pricem/da_platform/notes/ztex_pinout_aug16.xlsx

Sheet: v1
Iso interface pin name | Nexys2 port | ZTEX breakout pin | ZTEX FPGA pin
mclk | pmod3[1] | C24 | M4
amcs | pmod3[0] | C23 | N4
amdi | pmod3[2] | C25 | M3
amdo | pmod3[3] | C26 | M2
dmcs | pmod4[0] | C27 | K5
dmdi | pmod4[1] | C28 | L4
dmdo | pmod4[2] | C29 | L3
dirchan | pmod4[3] | C30 | K3
acon1 | pmod3[6] | D25 | R2
acon0 | pmod3[7] | D26 | P2
aovf | pmod3[5] | D24 | R1
clk0 | pmod4[4] | D27 | N2
reset_out | pmod4[7] | D30 | L1
srclk | pmod4[6] | D29 | M1
clksel | pmod4[5] | D28 | N1
clk1 | pmod3[4] | D23 | T1
slotdata1[5] | pmod2[0] | C19 | N6
slotdata1[4] | pmod2[1] | C20 | M6
slotdata1[3] | pmod1[2] | C14 | U2
slotdata1[2] | pmod1[3] | C15 | K6
slotdata1[1] | pmod1[0] | C12 | R5
slotdata1[0] | pmod1[1] | C13 | V2
slotdata0[5] | pmod2[5] | D20 | N5
slotdata0[4] | pmod2[4] | D19 | P5
slotdata0[3] | pmod1[7] | D15 | R3
slotdata0[2] | pmod1[6] | D14 | T3
slotdata0[1] | pmod1[5] | D13 | U1
slotdata0[0] | pmod1[4] | D12 | V1
slotdata3[5] |  | C6 | U6 | Unused signals
slotdata3[4] |  | D6 | V5
slotdata3[3] |  | C7 | T8
slotdata3[2] |  | D7 | V4
slotdata3[1] |  | C8 | R8
slotdata3[0] |  | D8 | T5
slotdata2[5] |  | C9 | R7
slotdata2[4] |  | D9 | T4
slotdata2[3] |  | C10 | T6
slotdata2[2] |  | D10 | U4
slotdata2[1] |  | C11 | R6
slotdata2[0] |  | D11 | U3
led_debug[3] |  | D4 | V7
led_debug[2] |  | C4 | U8
led_debug[1] |  | D3 | V9
led_debug[0] |  | C3 | U9
Notes:
- Make clk0/CLK1 clock capable

Sheet: v2
OLD pin name | OLD breakout pin | ALT pin name | ALT2 pin name | Iso interface pin name | Carrier conn pin | ZTEX breakout pin | ZTEX FPGA pin | Requirements
slotdata0[3] | D15 | slotdata0[1] | slotdata[1] | s0_lrck | 1 | A28 | B12
slotdata0[5] | D20 | slotdata0[0] | slotdata[0] | s0_bck | 2 | B28 | C12
 |  | slotdata0[3] | slotdata[3] | s0_d1 | 3 | A27 | B14
slotdata0[4] | D19 | slotdata0[2] | slotdata[2] | s0_d0 | 4 | B27 | B13
 |  | slotdata0[5] | slotdata[5] | s0_d3 | 5 | A26 | A16
 |  | slotdata0[4] | slotdata[4] | s0_d2 | 6 | B26 | A15
slotdata1[3] | C14 | slotdata1[1] | slotdata[7] | s1_lrck | 9 | A24 | C14 |  | OK
slotdata1[5] | C19 | slotdata1[0] | slotdata[6] | s1_bck | 10 | B24 | D14 |  | OK
 |  | slotdata1[3] | slotdata[9] | s1_d1 | 11 | A23 | B17
slotdata1[4] | C20 | slotdata1[2] | slotdata[8] | s1_d0 | 12 | B23 | B16 |  | OK
 |  | slotdata1[5] | slotdata[11] | s1_d3 | 13 | A22 | C15
 |  | slotdata1[4] | slotdata[10] | s1_d2 | 14 | B22 | D15
 |  | slotdata2[1] | slotdata[13] | s2_lrck | 17 | A20 | C17
 |  | slotdata2[0] | slotdata[12] | s2_bck | 18 | B20 | C16
 |  | slotdata2[3] | slotdata[15] | s2_d1 | 19 | A19 | E16
 |  | slotdata2[2] | slotdata[14] | s2_d0 | 20 | B19 | E15
 |  | slotdata2[5] | slotdata[17] | s2_d3 | 21 | A18 | F13
 |  | slotdata2[4] | slotdata[16] | s2_d2 | 22 | B18 | F14
 |  | slotdata3[1] | slotdata[19] | s3_lrck | 25 | A14 | G13
 |  | slotdata3[0] | slotdata[18] | s3_bck | 26 | B14 | D17
 |  | slotdata3[3] | slotdata[21] | s3_d1 | 27 | A13 | D18
 |  | slotdata3[2] | slotdata[20] | s3_d0 | 28 | B13 | E17
 |  | slotdata3[5] | slotdata[23] | s3_d3 | 29 | A12 | E18
 |  | slotdata3[4] | slotdata[22] | s3_d2 | 30 | B12 | F15
 |  |  |  | hwflag | 33 | A11 | F18
 |  |  |  | hwcon | 34 | B11 | F16
dmcs | C27 |  |  | cs_n | 35 | A9 | G17 |  | OK
dirchan | C30 |  |  | dirchan | 36 | B9 | G16 |  | OK
 |  |  |  | srclk2 | 37 | A8 | H17
srclk | D29 |  |  | srclk | 38 | B8 | G14 |  | OK
dmdi | C28 |  |  | mosi | 39 | A7 | J14 |  | OK - needed fix
dmdo | C29 |  |  | miso | 40 | B7 | H14 |  | OK
clksel | D28 |  |  | clksel | 42 | B6 | J13 |  | OK
mclk | C24 |  |  | sclk | 43 | A5 | J15 |  | OK - needed fix
reset_out | D30 |  |  | reset_n | 44 | B5 | K13 |  | OK
clk0 | D27 |  |  | mclk | 47 | B10 | H16 | CC | OK
 |  |  |  |  | Note: increasing pin number on carrier -> increasing number on FPGA

Sheet: v2 (before fix)
Iso interface pin name | Carrier connector pin | ZTEX breakout pin | ZTEX FPGA pin | Requirements
s0_lrck | 1 | D5
s0_bck | 2 | C5
s0_d1 | 3 | D6
s0_d0 | 4 | C6
s0_d3 | 5 | D7
s0_d2 | 6 | C7
s1_lrck | 9 | D9
s1_bck | 10 | C9
s1_d1 | 11 | D10
s1_d0 | 12 | C10
s1_d3 | 13 | D11
s1_d2 | 14 | C11
s2_lrck | 17 | D13
s2_bck | 18 | C13
s2_d1 | 19 | D14
s2_d0 | 20 | C14
s2_d3 | 21 | D15
s2_d2 | 22 | C15
s3_lrck | 25 | D19
s3_bck | 26 | C19
s3_d1 | 27 | D21
s3_d0 | 28 | C21
s3_d3 | 29 | D22
s3_d2 | 30 | C22
hwflag | 33 | D23
hwcon | 34 | C23
cs_n | 35 | D24
dirchan | 36 | C24
srclk2 | 37 | D25
srclk | 38 | C25
mosi | 39 | D26
miso | 40 | C26
clksel | 42 | C27
sclk | 43 | D28
reset_n | 44 | C28
mclk | 47 | D20 | N5 | CC
 | Note: increasing pin number on carrier -> increasing number on FPGA
