pricem/da_platform/docs/figures/dac8_adc8_loopback_fr.pdf

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

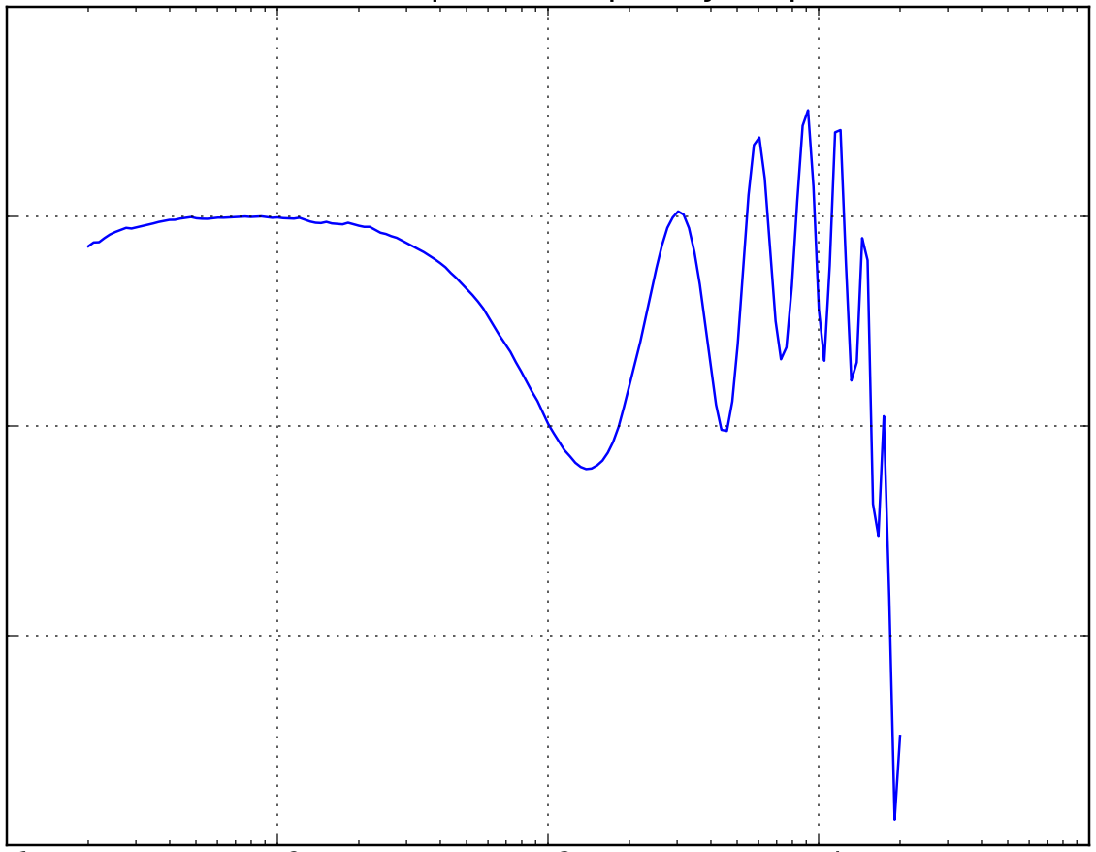
[picture p9: figure]
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
