pricem/da_platform/docs/photos/DSC_0177.JPG

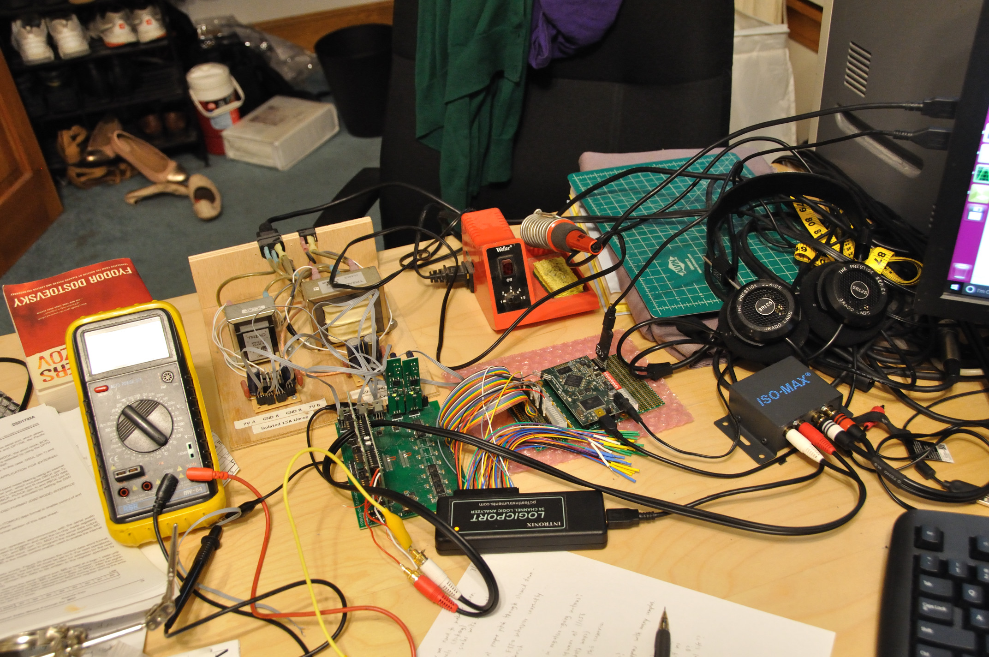
docs/photos/DSC_0177.JPG
