pricem/da_platform/docs/photos/DSC_0237.jpg

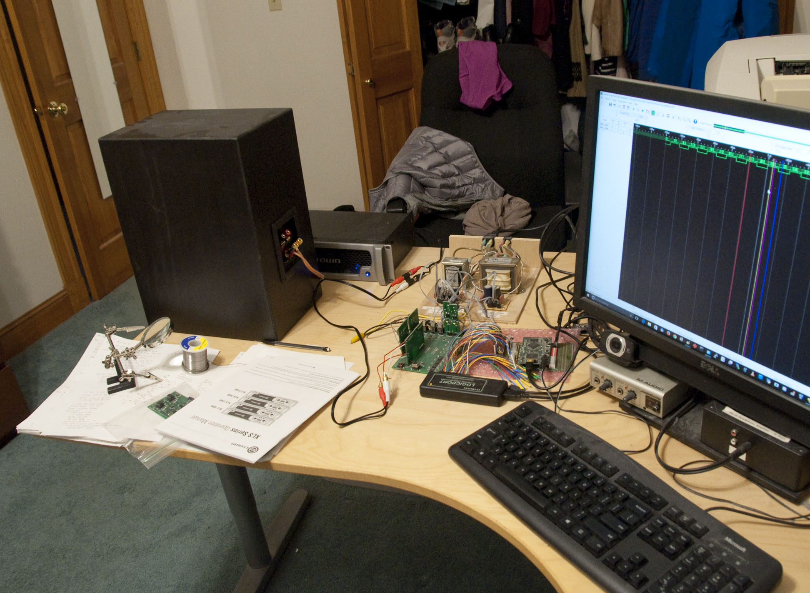
docs/photos/DSC_0237.jpg
