pricem/da_platform/docs/photos/DSC_0237_01.JPG

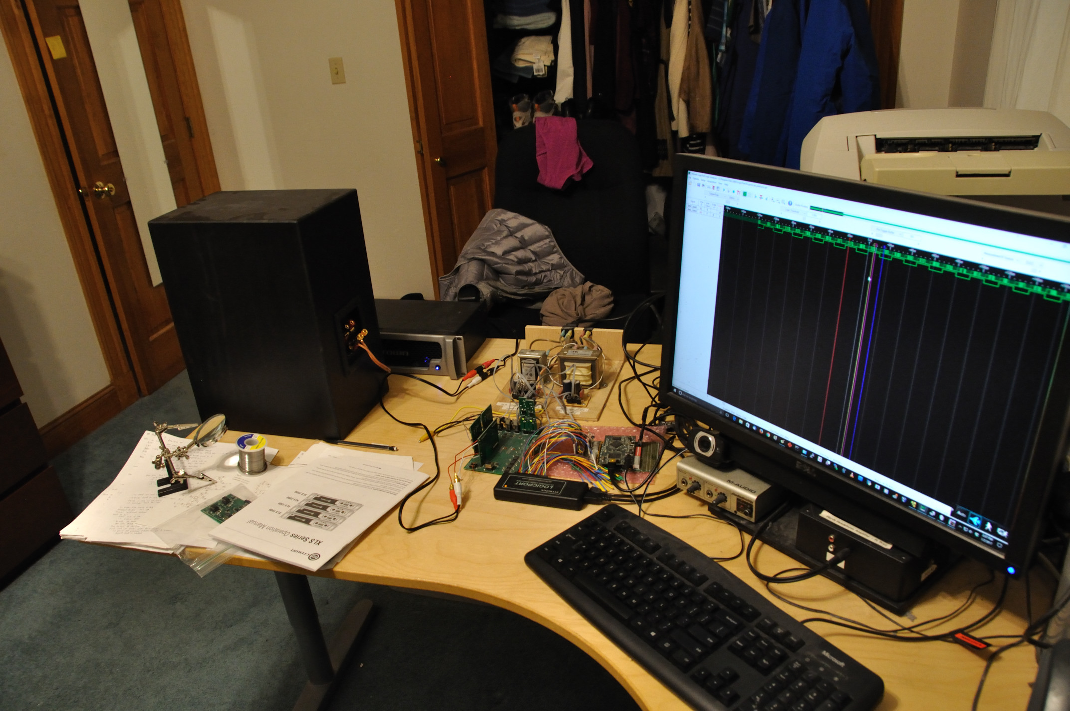
docs/photos/DSC_0237_01.JPG
