pricem/da_platform/docs/photos/DSC_0239.jpg

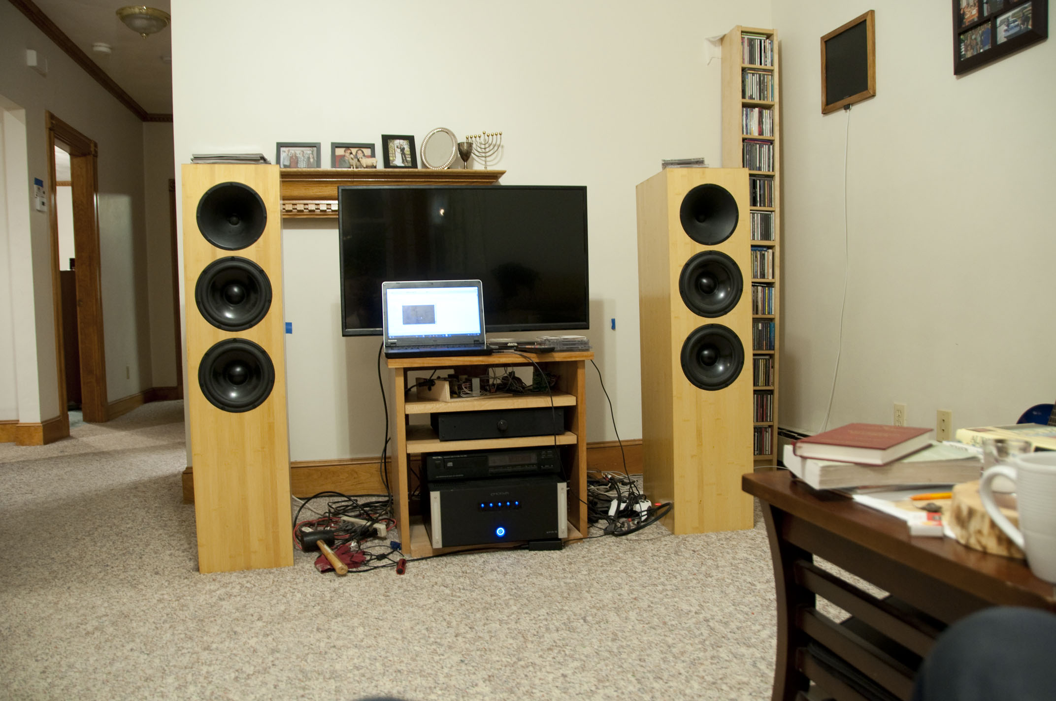
docs/photos/DSC_0239.jpg
