pricem/da_platform/docs/photos/DSC_0240.jpg

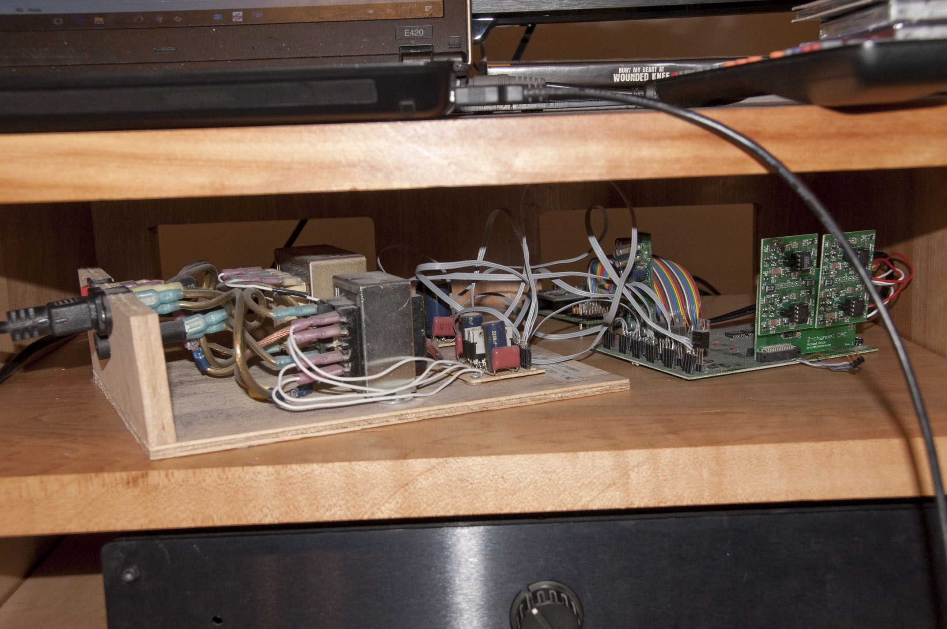
docs/photos/DSC_0240.jpg
