pricem/da_platform/docs/photos/DSC_0240_01.JPG

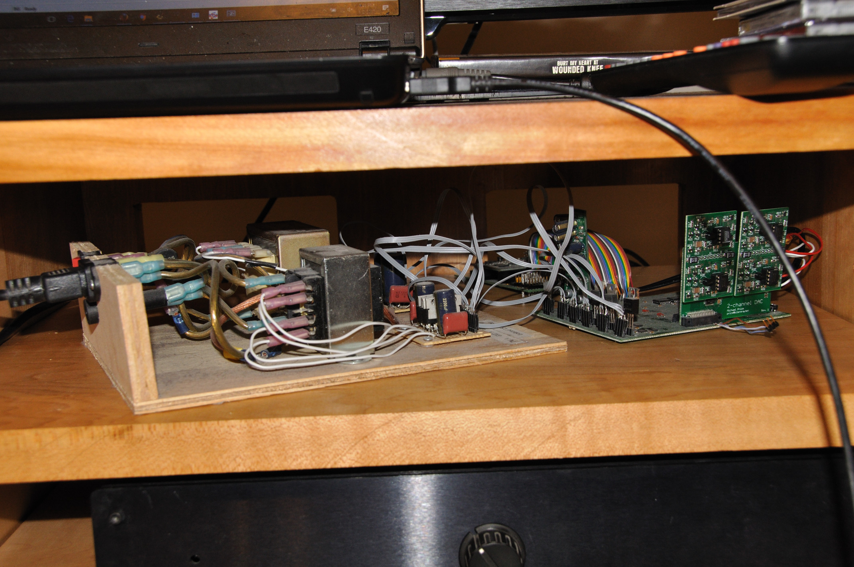
docs/photos/DSC_0240_01.JPG
