pricem/da_platform/docs/photos/DSC_0245.JPG

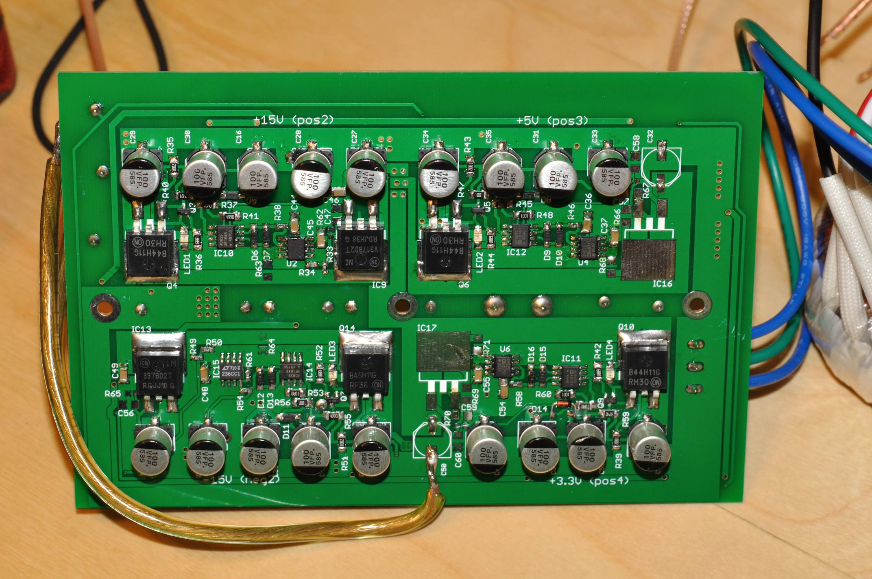
docs/photos/DSC_0245.JPG
