pricem/da_platform/docs/photos/DSC_0246.JPG

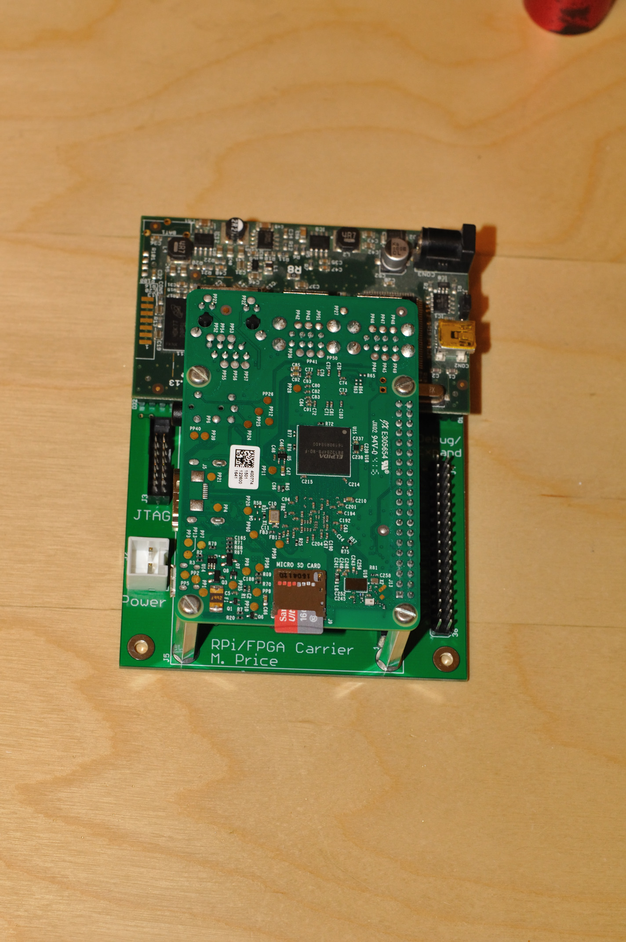
docs/photos/DSC_0246.JPG
