pricem/da_platform/docs/photos/DSC_0248.JPG

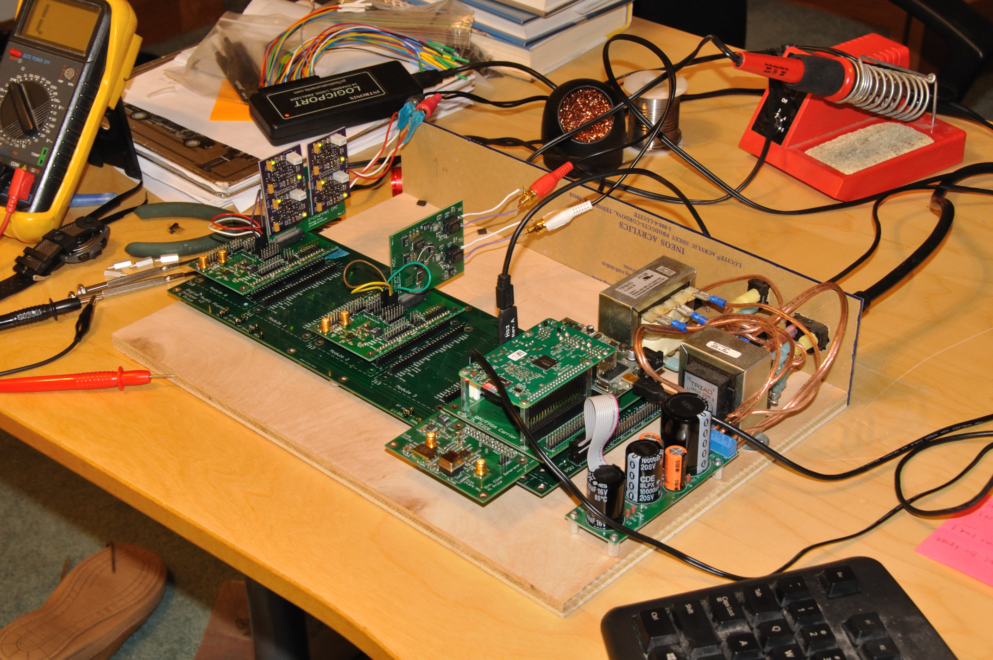
docs/photos/DSC_0248.JPG
