pricem/da_platform/docs/photos/DSC_0252_01.JPG

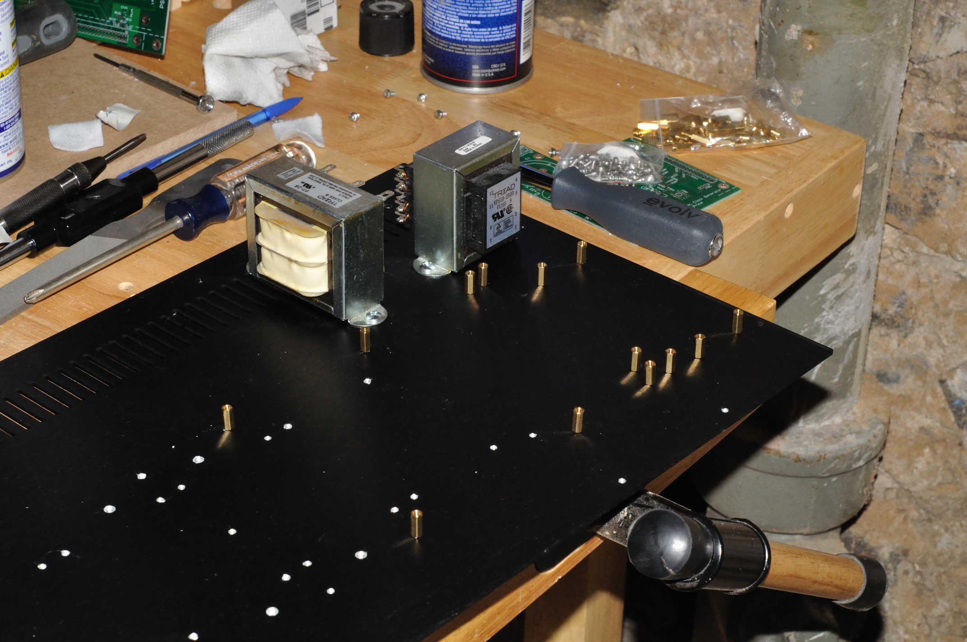
docs/photos/DSC_0252_01.JPG
