pricem/da_platform/docs/photos/DSC_0255.JPG

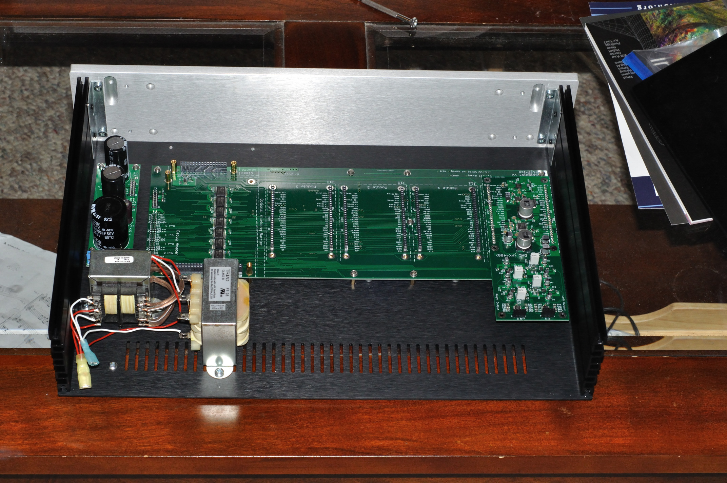
docs/photos/DSC_0255.JPG
