pricem/da_platform/docs/photos/DSC_0258.JPG

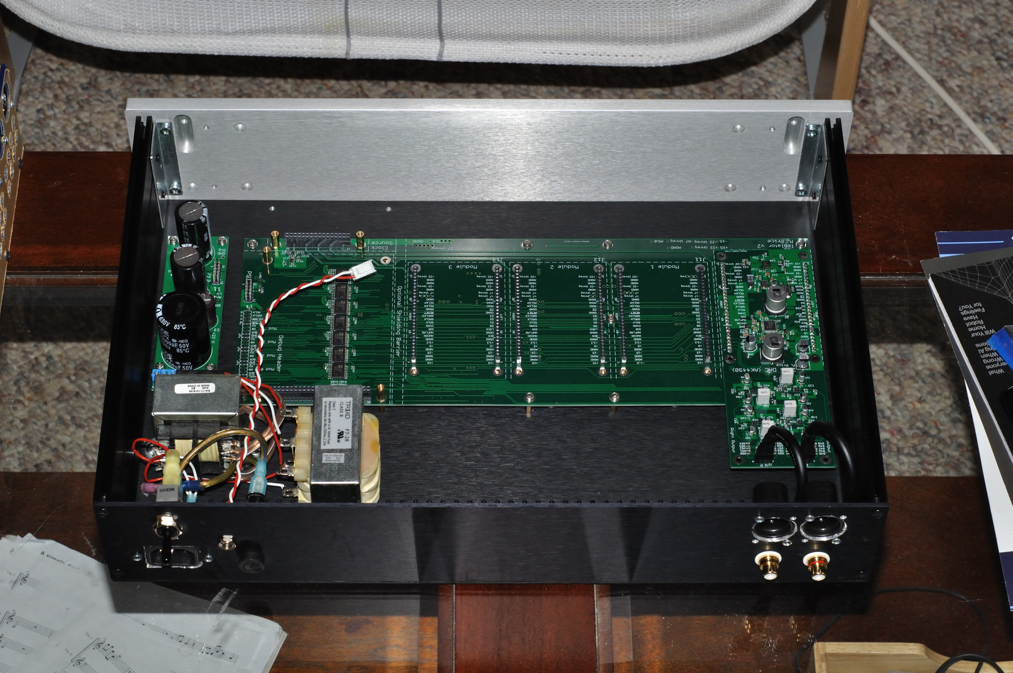
docs/photos/DSC_0258.JPG
