pricem/da_platform/docs/photos/DSC_0274.JPG

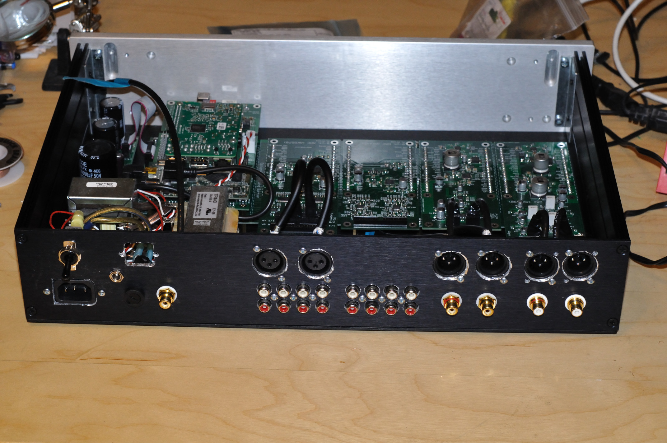
docs/photos/DSC_0274.JPG
