pricem/da_platform/docs/photos/DSC_0276.JPG

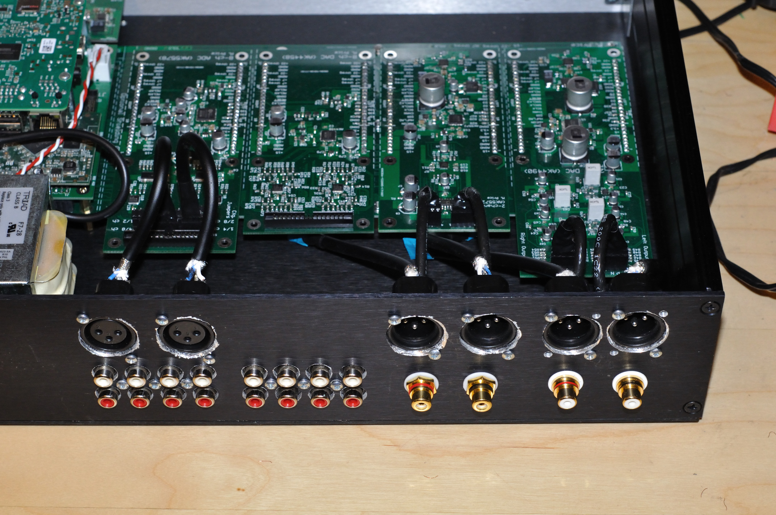
docs/photos/DSC_0276.JPG
