pricem/da_platform/docs/photos/DSC_0278.JPG

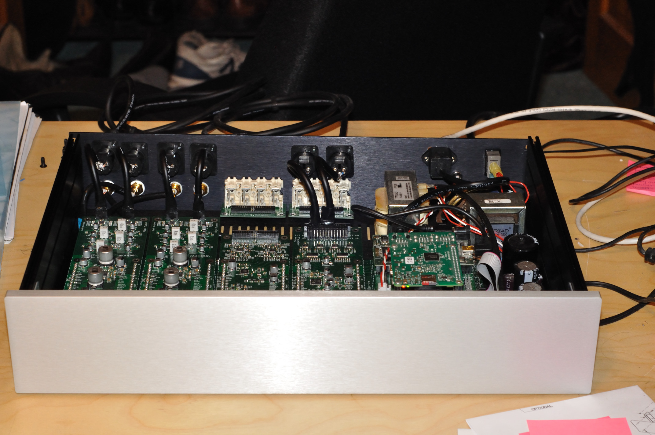
docs/photos/DSC_0278.JPG
