pricem/da_platform/docs/photos/DSC_0279.JPG

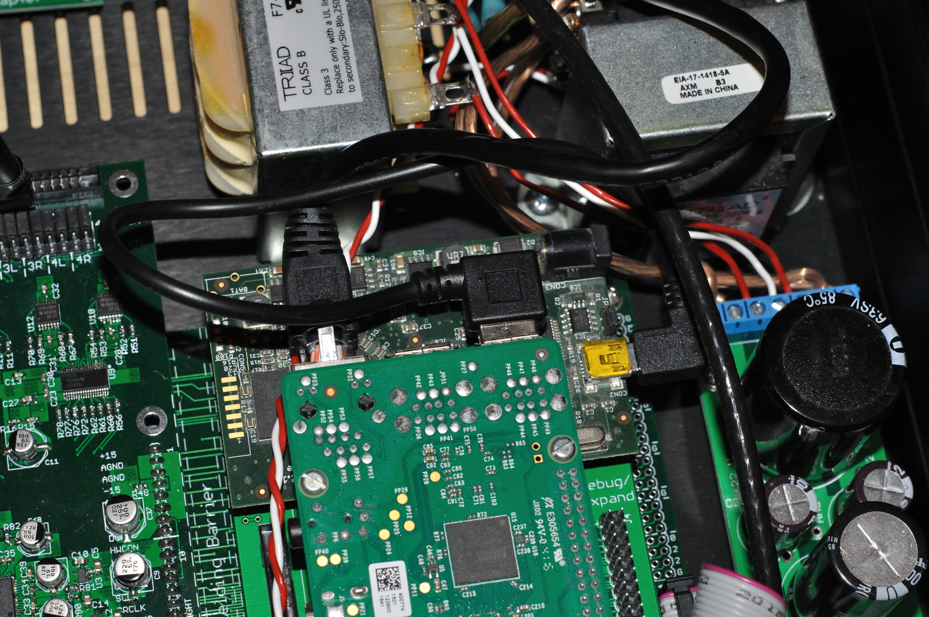
docs/photos/DSC_0279.JPG
