pricem/da_platform/docs/photos/DSC_0280.JPG

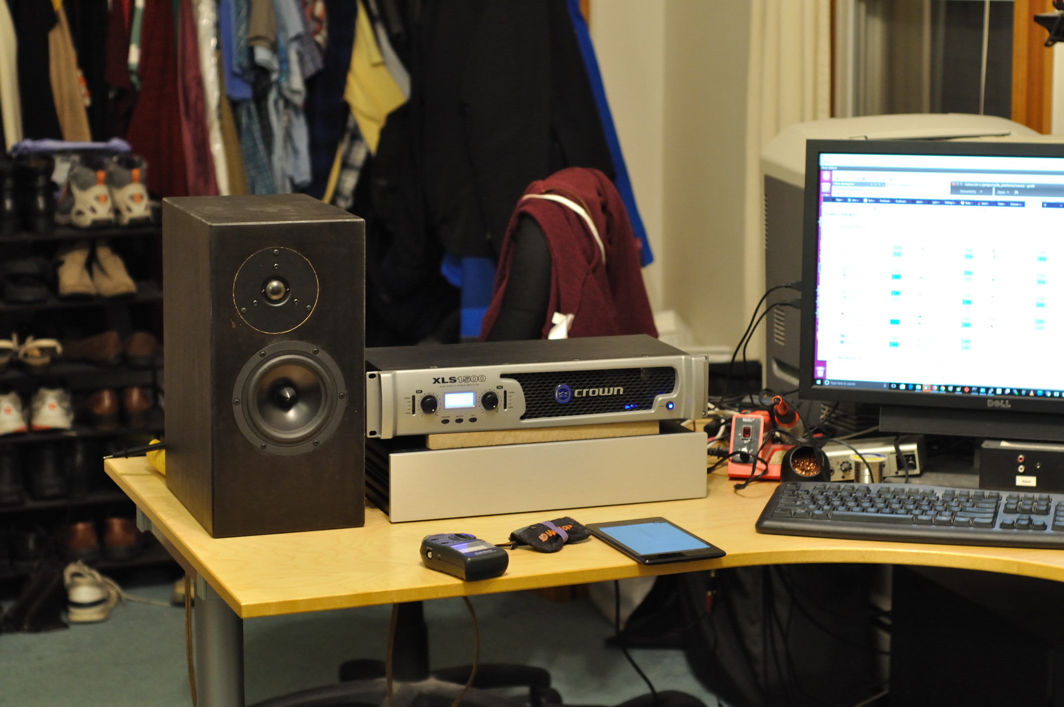
docs/photos/DSC_0280.JPG
