pricem/da_platform/docs/photos/DSC_0281.JPG

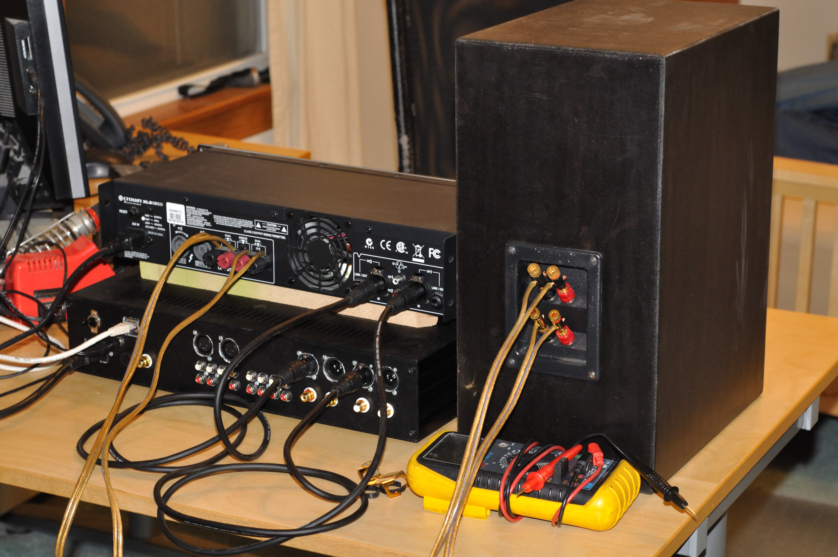
docs/photos/DSC_0281.JPG
