pricem/da_platform/docs/photos/indiv_boards/adc2_v2p1.jpg

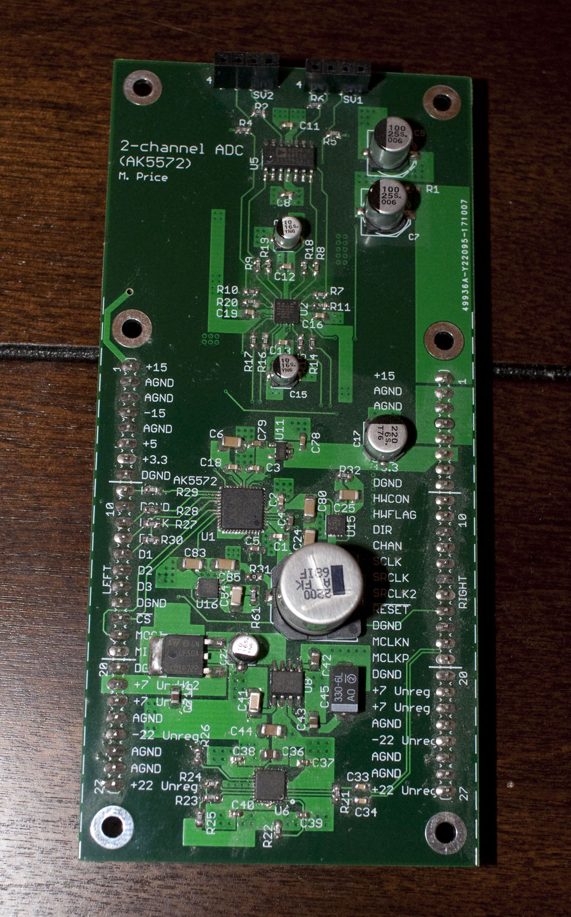
docs/photos/indiv_boards/adc2_v2p1.jpg
