pricem/da_platform/docs/photos/indiv_boards/backplane_lowcost.jpg

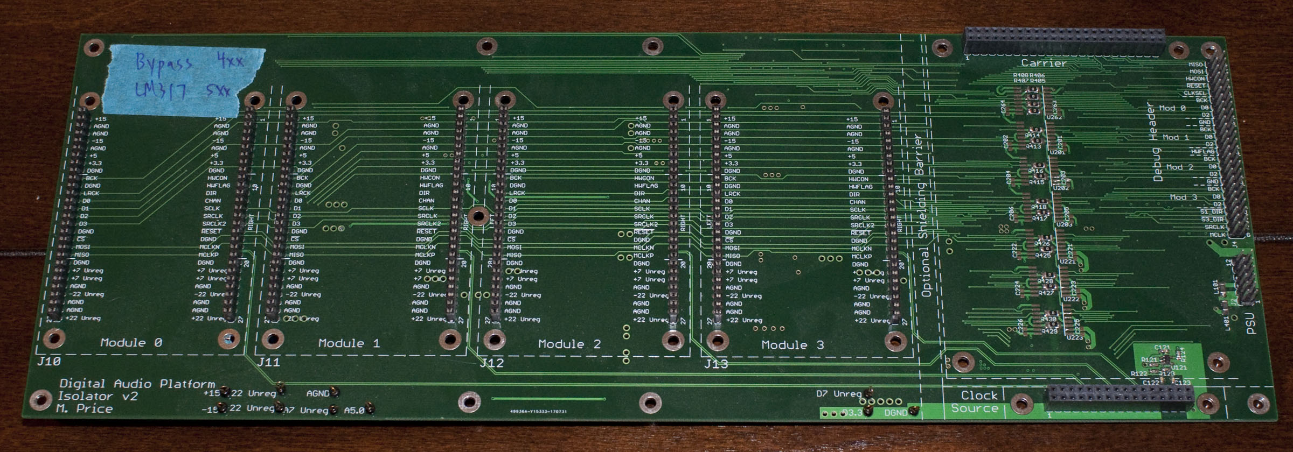
docs/photos/indiv_boards/backplane_lowcost.jpg
