pricem/da_platform/docs/schematics/dac2_v1_iv_b.pdf

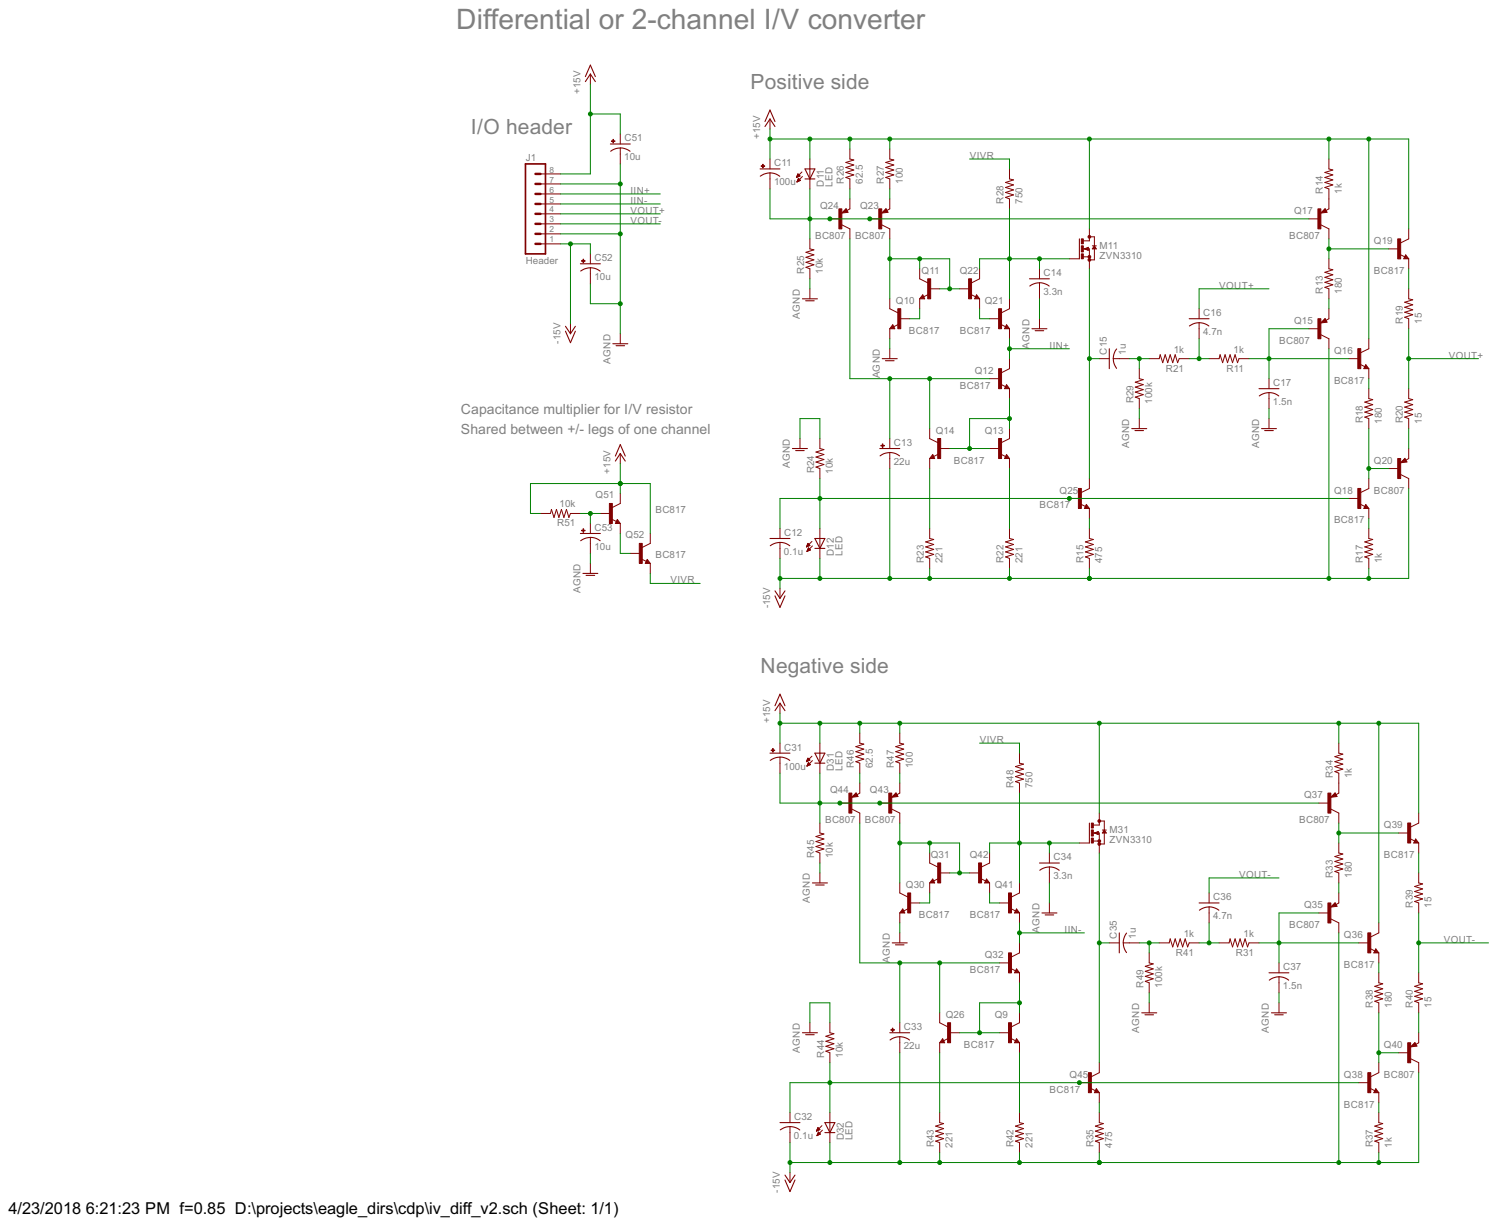
[picture p57: page 1]

Differential or 2-channel I/V converter

Capacitance multiplier for I/V resistor
Shared between +/- legs of one channel

4/23/2018 6:21:23 PM f=0.85 D:\projects\eagle_dirs\cdp\iv_diff_v2.sch (Sheet: 1/1)
