pricem/da_platform/docs/schematics/dac2_v2.pdf

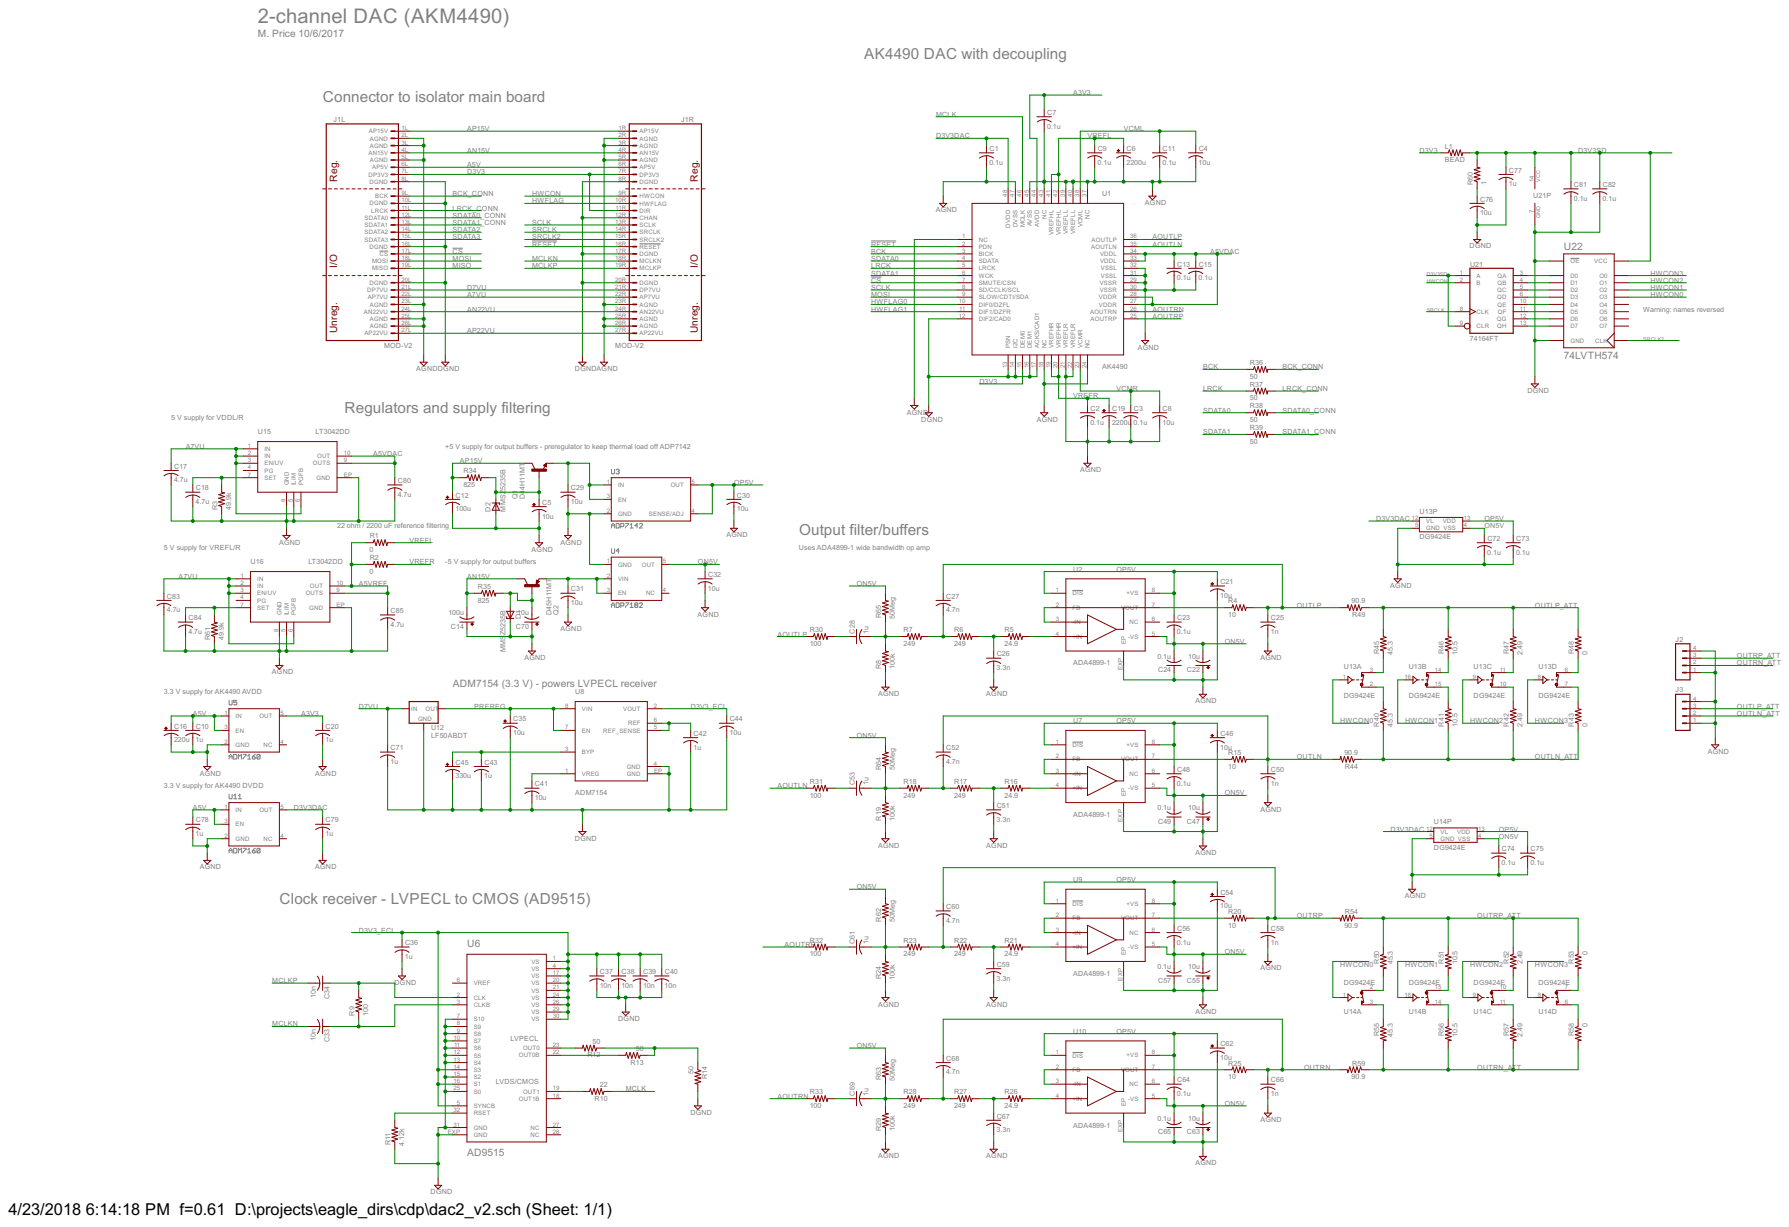
[picture p58: page 1]

Connector to isolator main board

7L AP5V | D3V3 | 7R
8L DP3V3 | | | 8R

14L SDATA1
15L SDATA2

Regulators and supply filtering

+5 V supply for output buffers - preregulator to keep thermal load off ADP7142

22 ohm / 2200 uF reference filtering

Clock receiver - LVPECL to CMOS (AD9515)

4/23/2018 6:14:18 PM f=0.61 D:\projects\eagle_dirs\cdp\dac2_v2.sch (Sheet: 1/1)
