pricem/da_platform/docs/schematics/dac8_v1_scaler_a.pdf

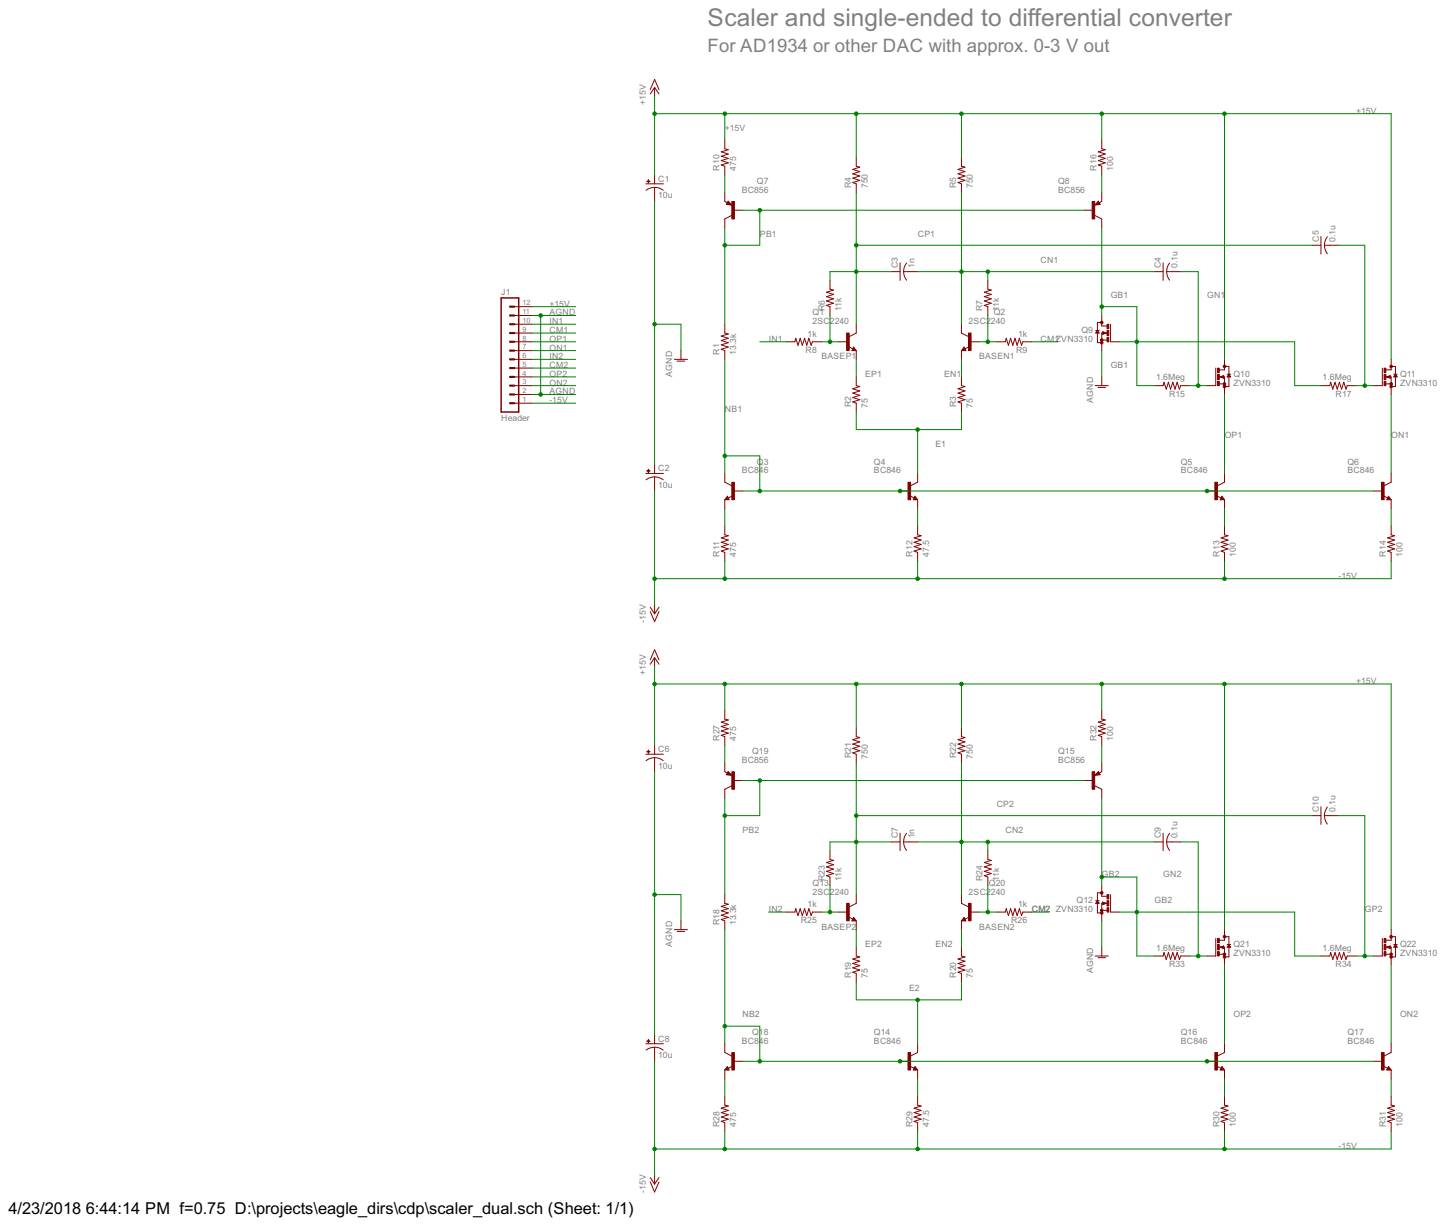
[picture p59: page 1]

Scaler and single-ended to differential converter
For AD1934 or other DAC with approx. 0-3 V out

4/23/2018 6:44:14 PM f=0.75 D:\projects\eagle_dirs\cdp\scaler_dual.sch (Sheet: 1/1)
