pricem/da_platform/docs/schematics/dac8_v1_scaler_b.pdf

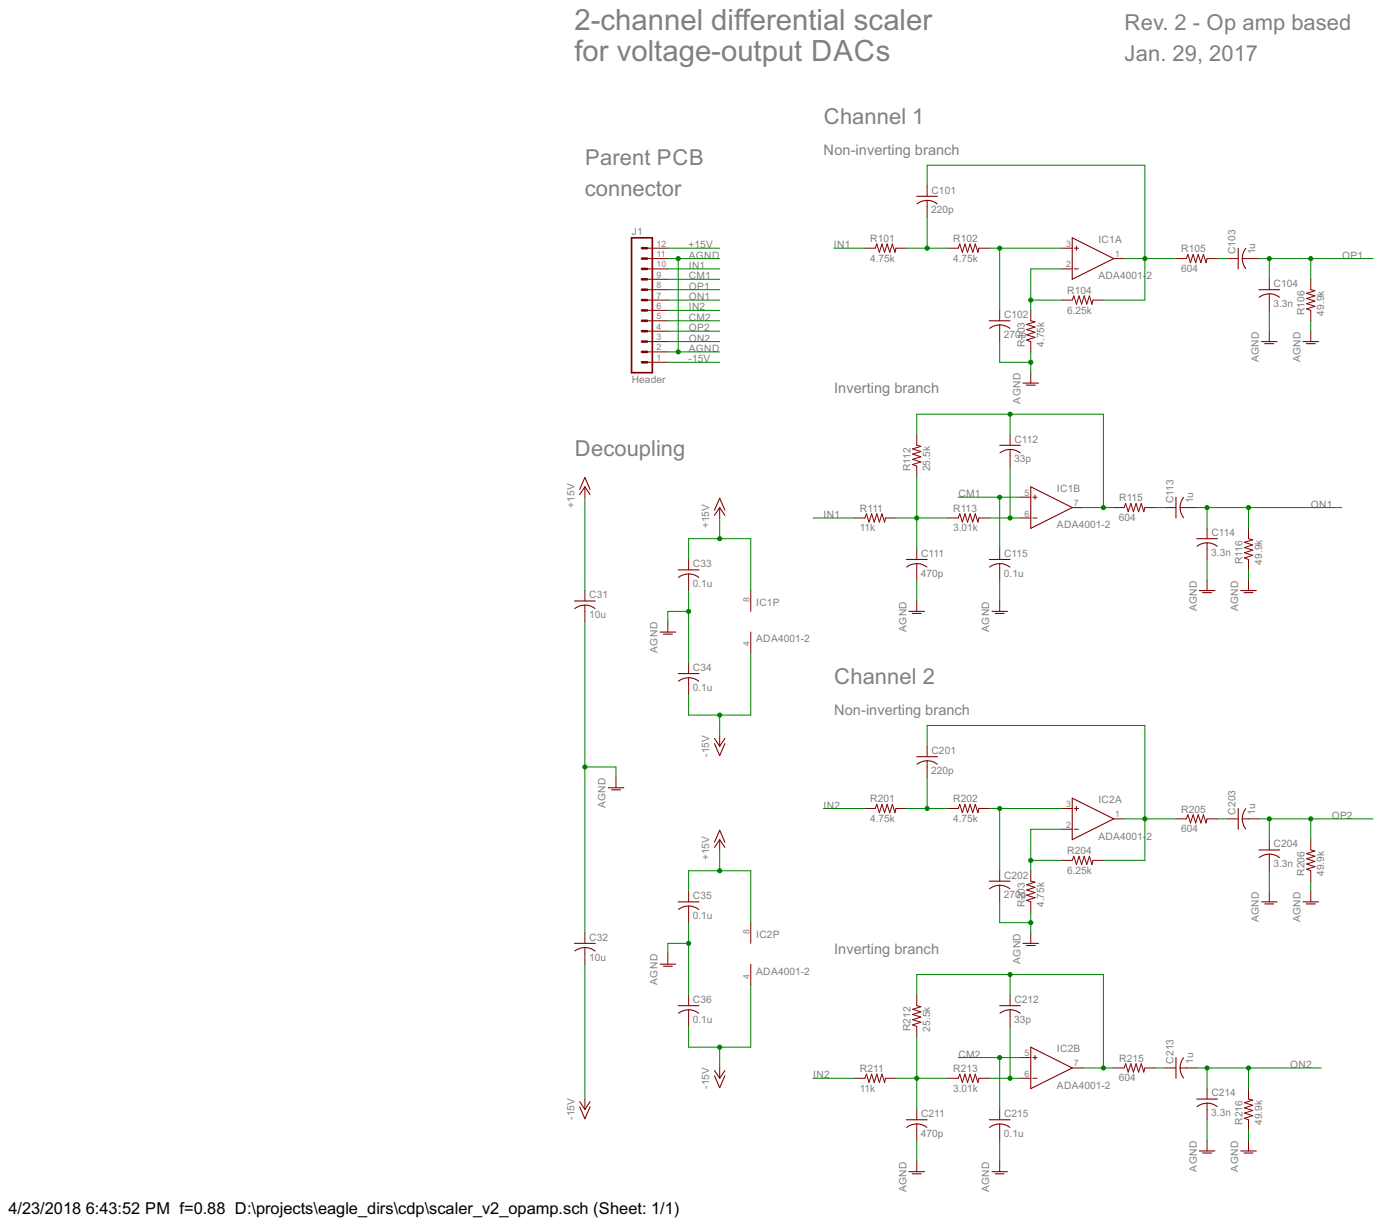
[picture p60: page 1]

2-channel differential scaler
for voltage-output DACs

Rev. 2 - Op amp based
Jan. 29, 2017

4/23/2018 6:43:52 PM f=0.88 D:\projects\eagle_dirs\cdp\scaler_v2_opamp.sch (Sheet: 1/1)
