pricem/da_platform/docs/schematics/dac8_v2.pdf

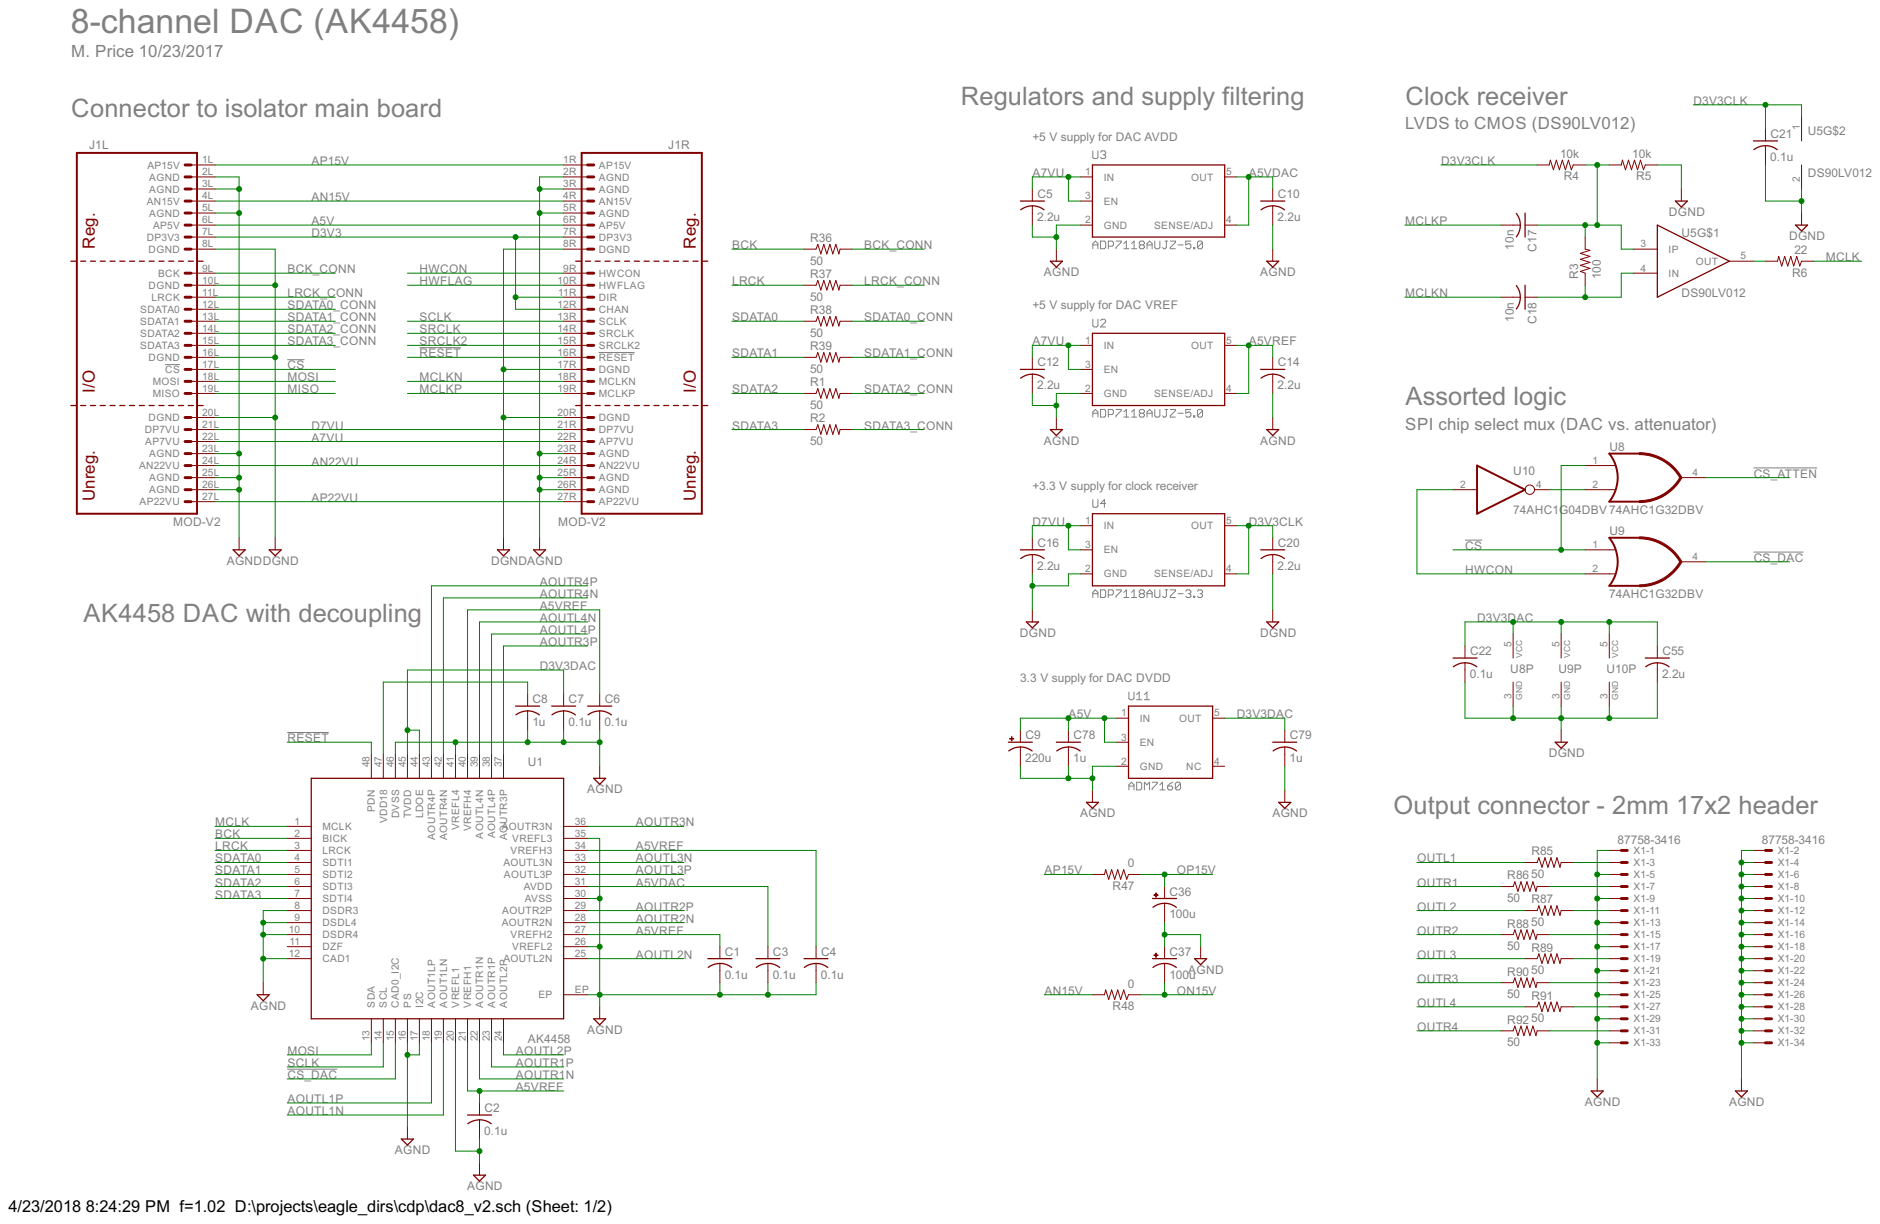
[picture p61: page 1]

+5 V supply for DAC AVDD

+5 V supply for DAC VREF

SPI chip select mux (DAC vs. attenuator)

+3.3 V supply for clock receiver

3.3 V supply for DAC DVDD

33 VREFH3 32 AOUTL3N 31 AOUTL3P | AOUTL3N AOUTL3P A5VDAC

30 AVDD | AOUTR2P AOUTR2N A5VREF

4/23/2018 8:24:29 PM f=1.02 D:\projects\eagle_dirs\cdp\dac8_v2.sch (Sheet: 1/2)

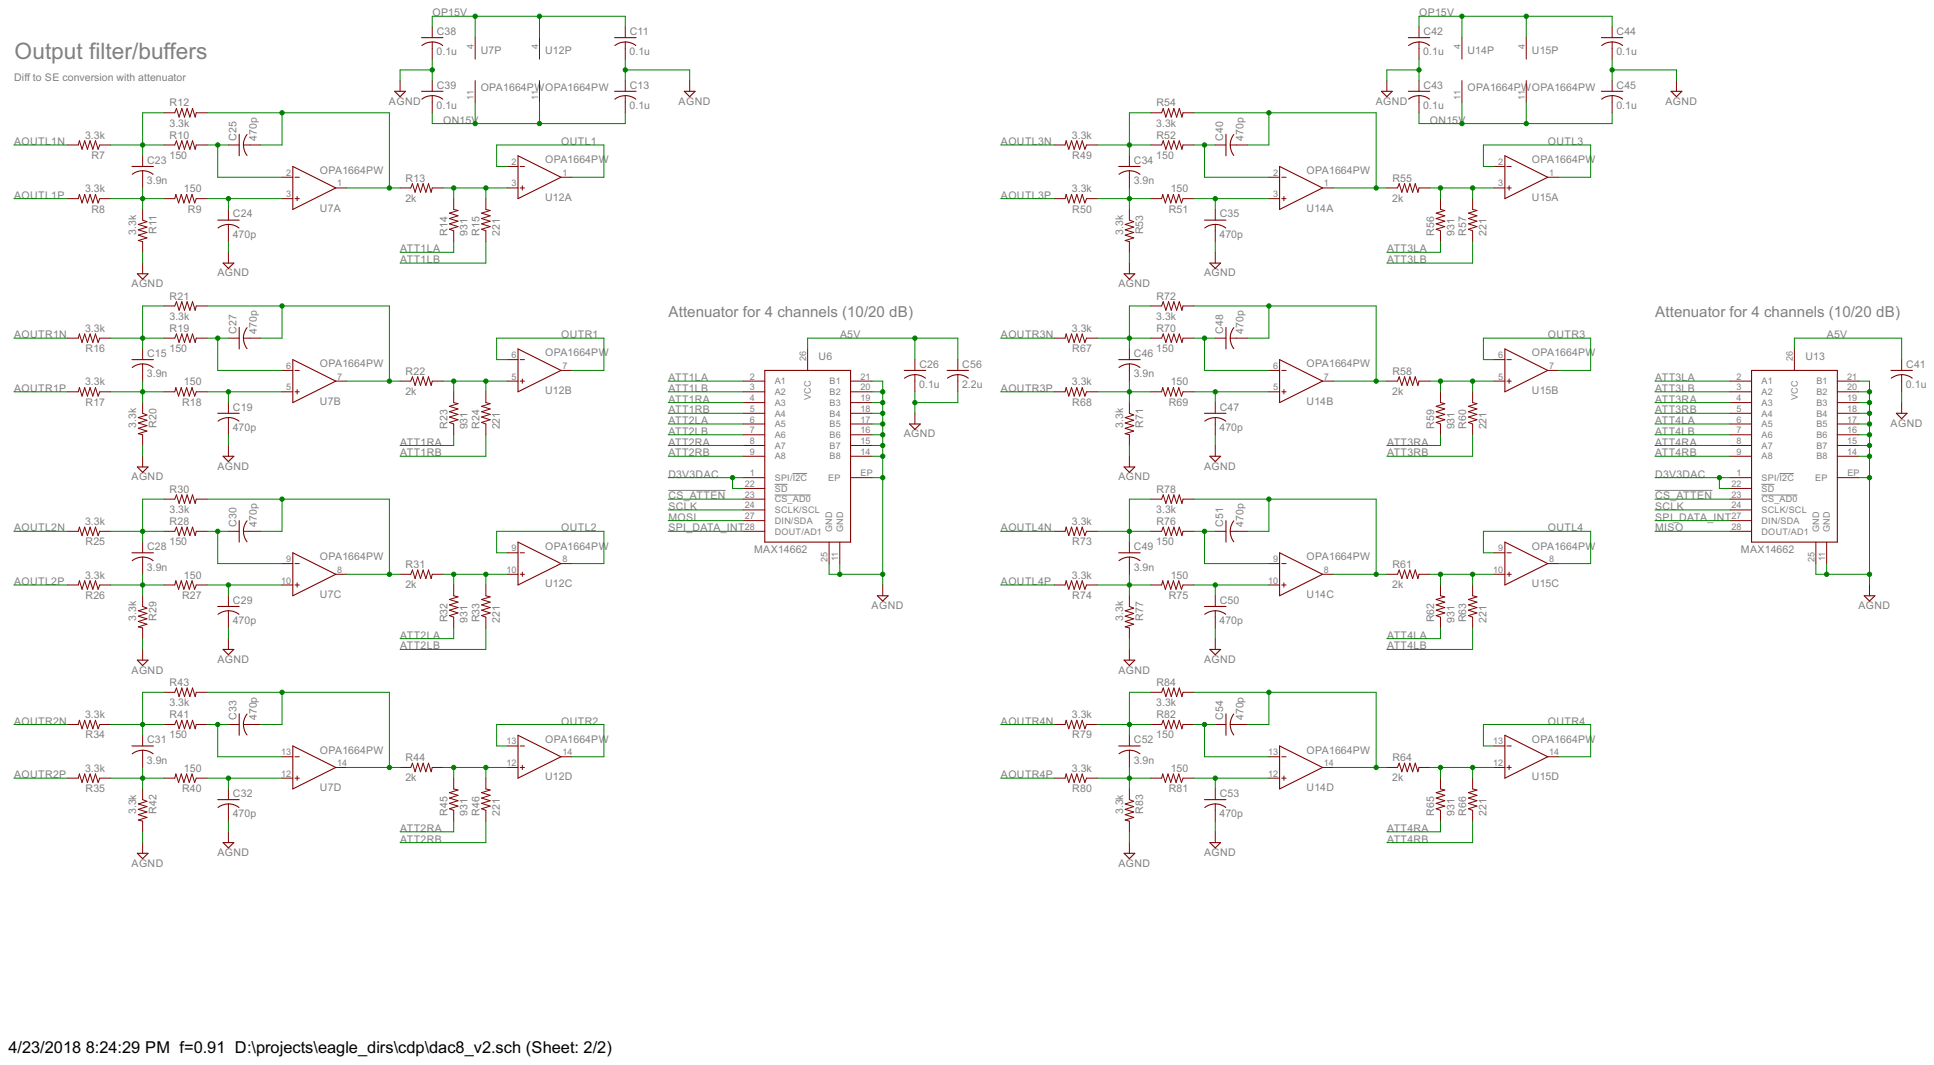
[picture p62: page 2]

Diff to SE conversion with attenuator

4/23/2018 8:24:29 PM f=0.91 D:\projects\eagle_dirs\cdp\dac8_v2.sch (Sheet: 2/2)
