pricem/da_platform/docs/schematics/isolator_v2.pdf

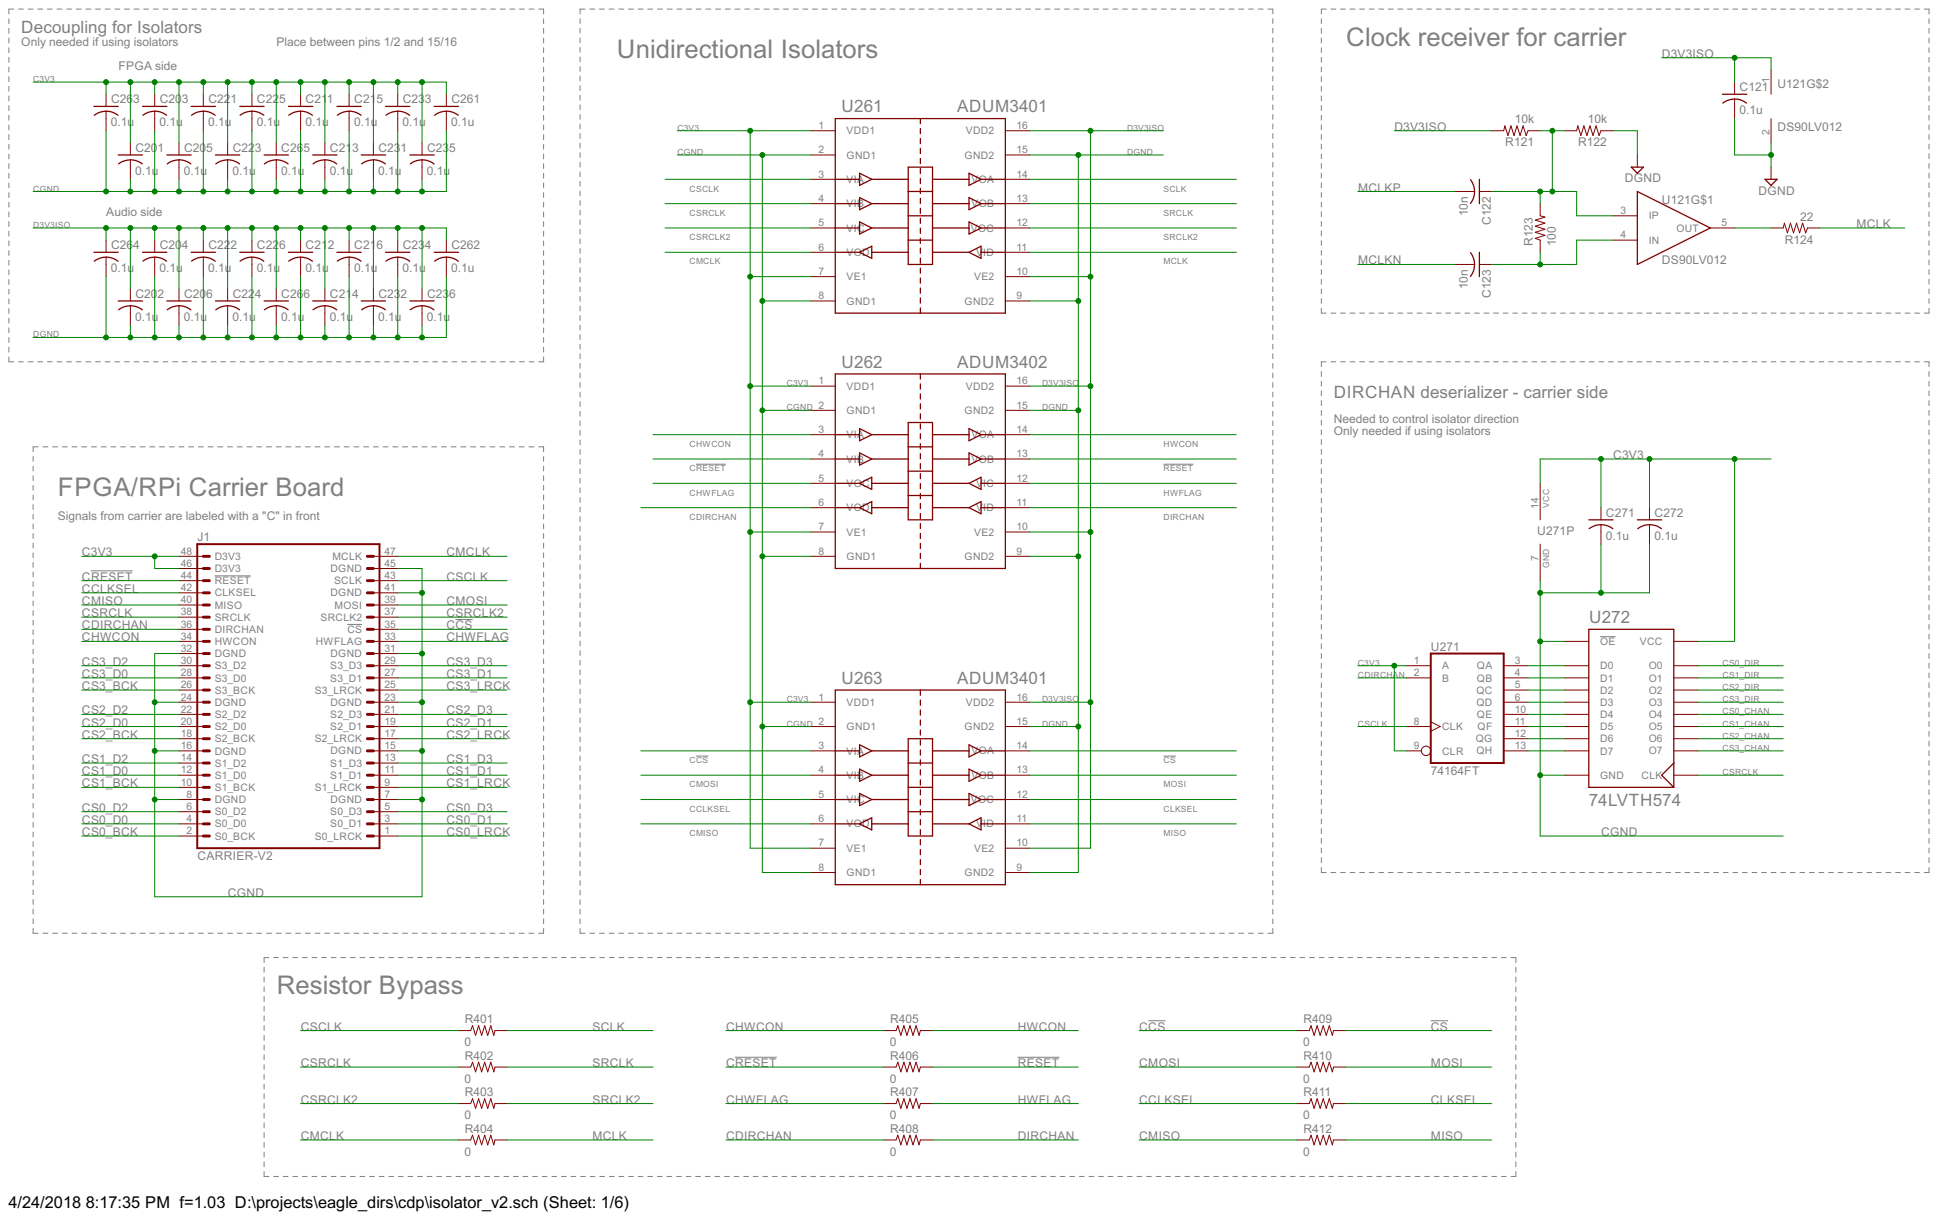
[picture p63: page 1]

DIRCHAN deserializer - carrier side

Needed to control isolator direction
Only needed if using isolators

FPGA/RPi Carrier Board

Signals from carrier are labeled with a "C" in front

4/24/2018 8:17:35 PM f=1.03 D:\projects\eagle_dirs\cdp\isolator_v2.sch (Sheet: 1/6)

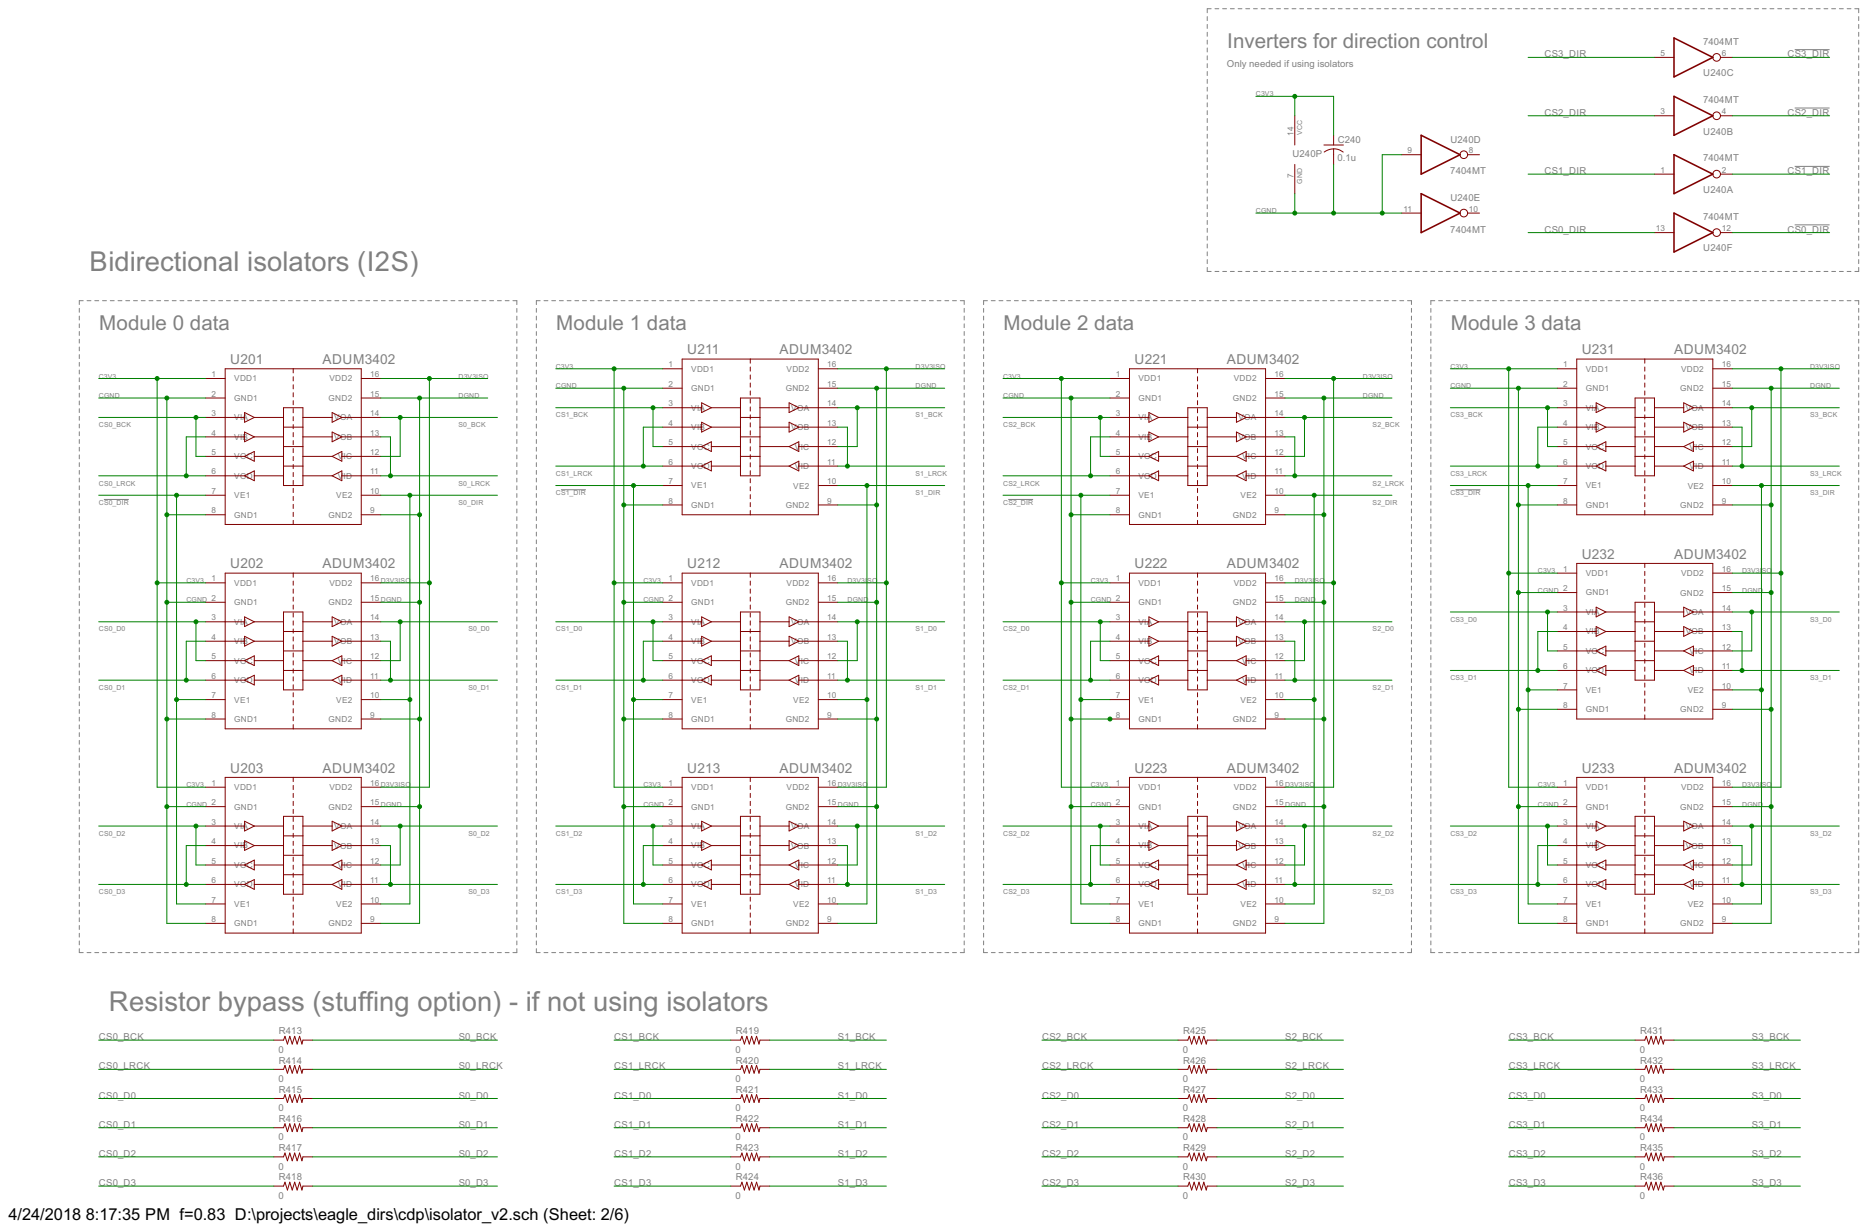
[picture p64: page 2]

Inverters for direction control

Only needed if using isolators

Resistor bypass (stuffing option) - if not using isolators

4/24/2018 8:17:35 PM f=0.83 D:\projects\eagle_dirs\cdp\isolator_v2.sch (Sheet: 2/6)

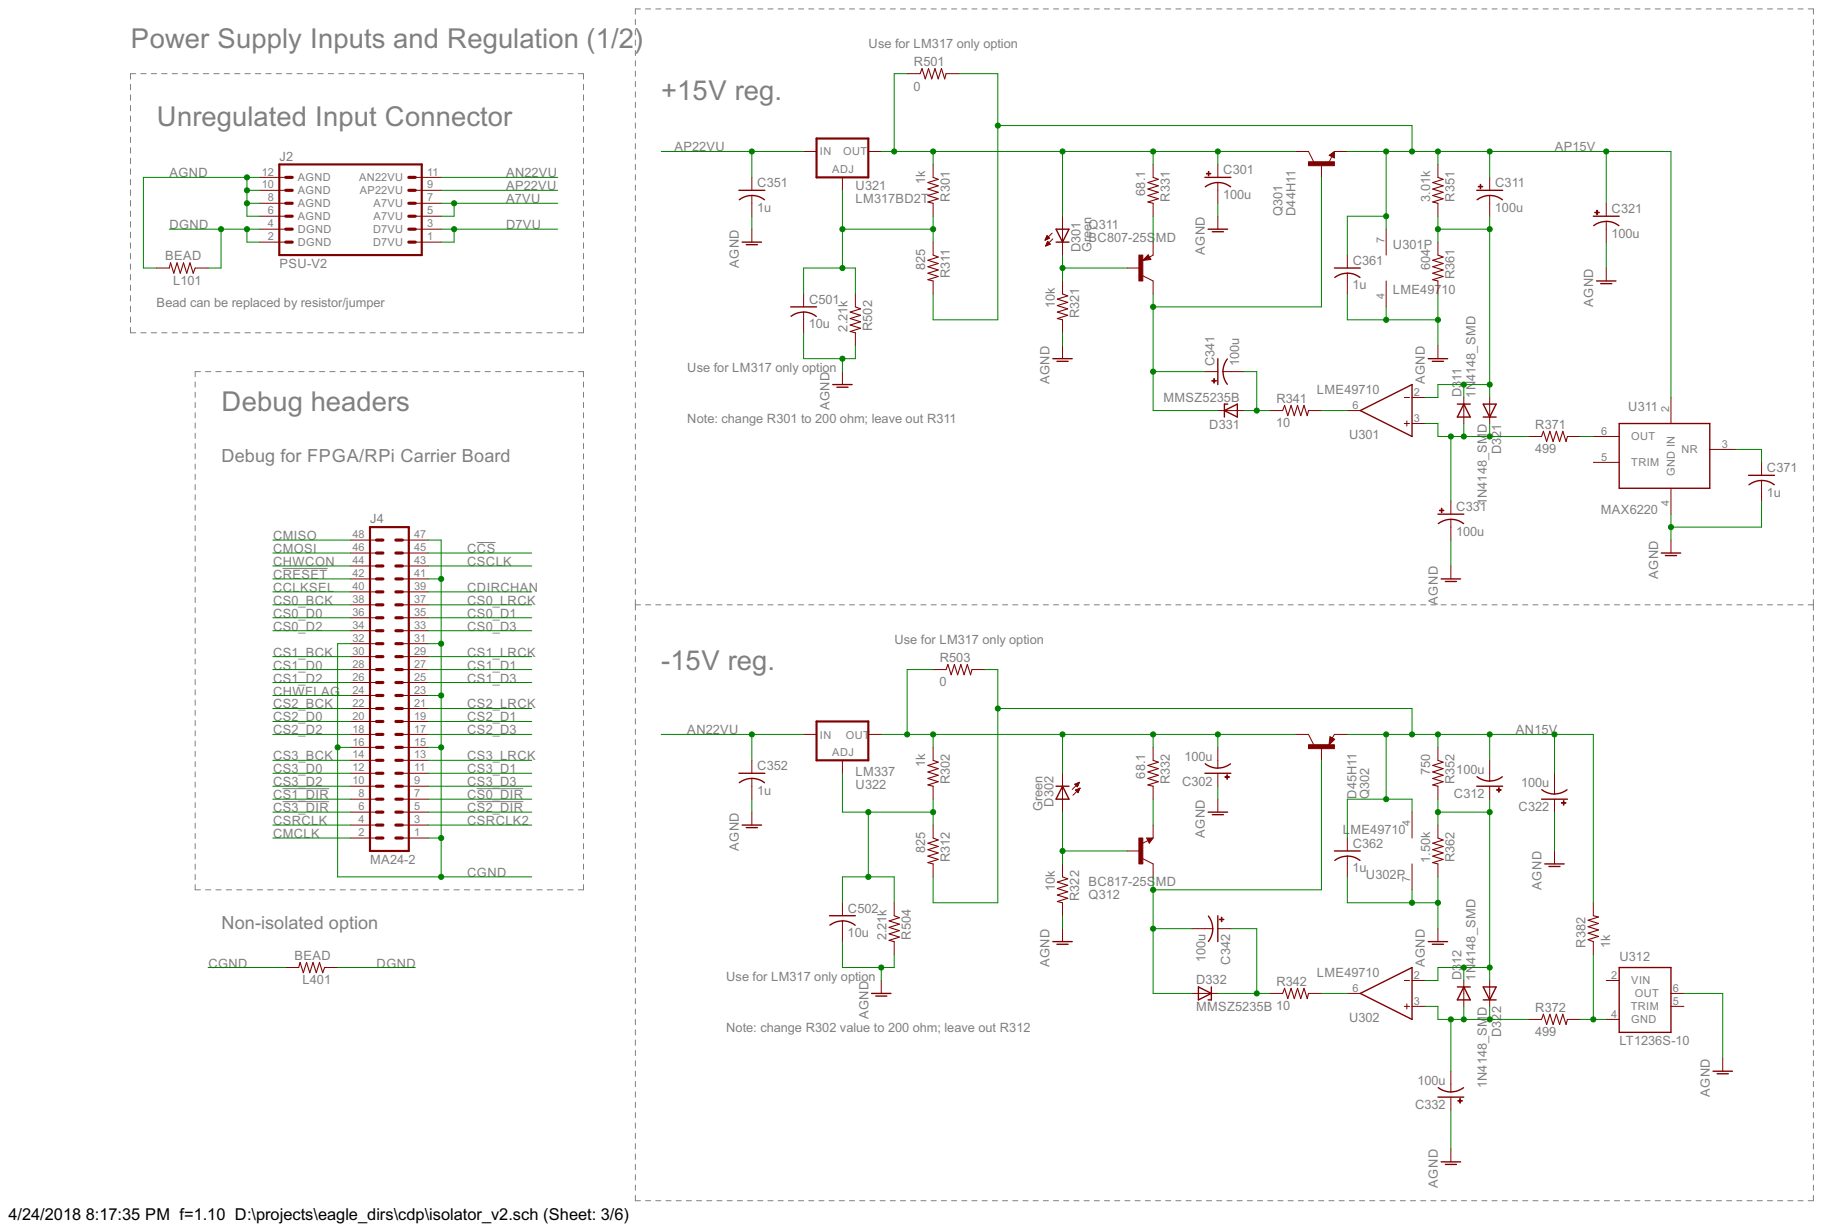
[picture p65: page 3]

Power Supply Inputs and Regulation (1/2)

Bead can be replaced by resistor/jumper

Use for LM317 only option Note: change R301 to 200 ohm; leave out R311

Debug for FPGA/RPi Carrier Board

Use for LM317 only option Note: change R302 value to 200 ohm; leave out R312

4/24/2018 8:17:35 PM f=1.10 D:\projects\eagle_dirs\cdp\isolator_v2.sch (Sheet: 3/6)

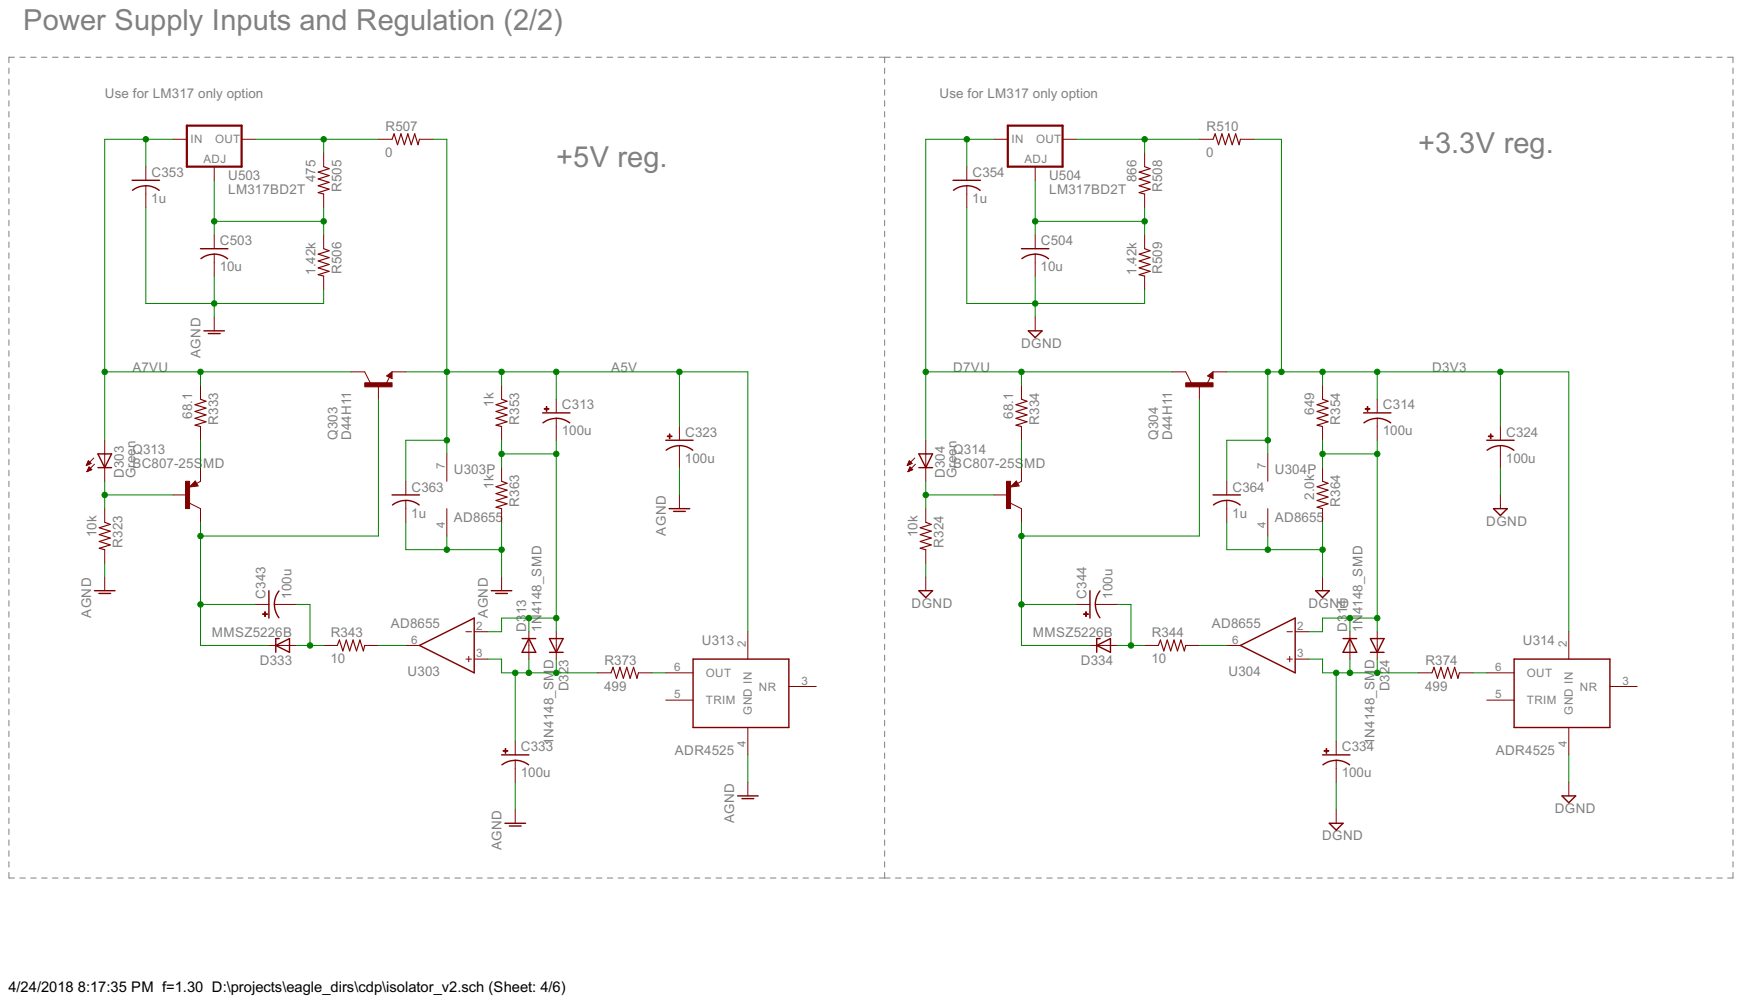
[picture p66: page 4]

Power Supply Inputs and Regulation (2/2)

4/24/2018 8:17:35 PM f=1.30 D:\projects\eagle_dirs\cdp\isolator_v2.sch (Sheet: 4/6)

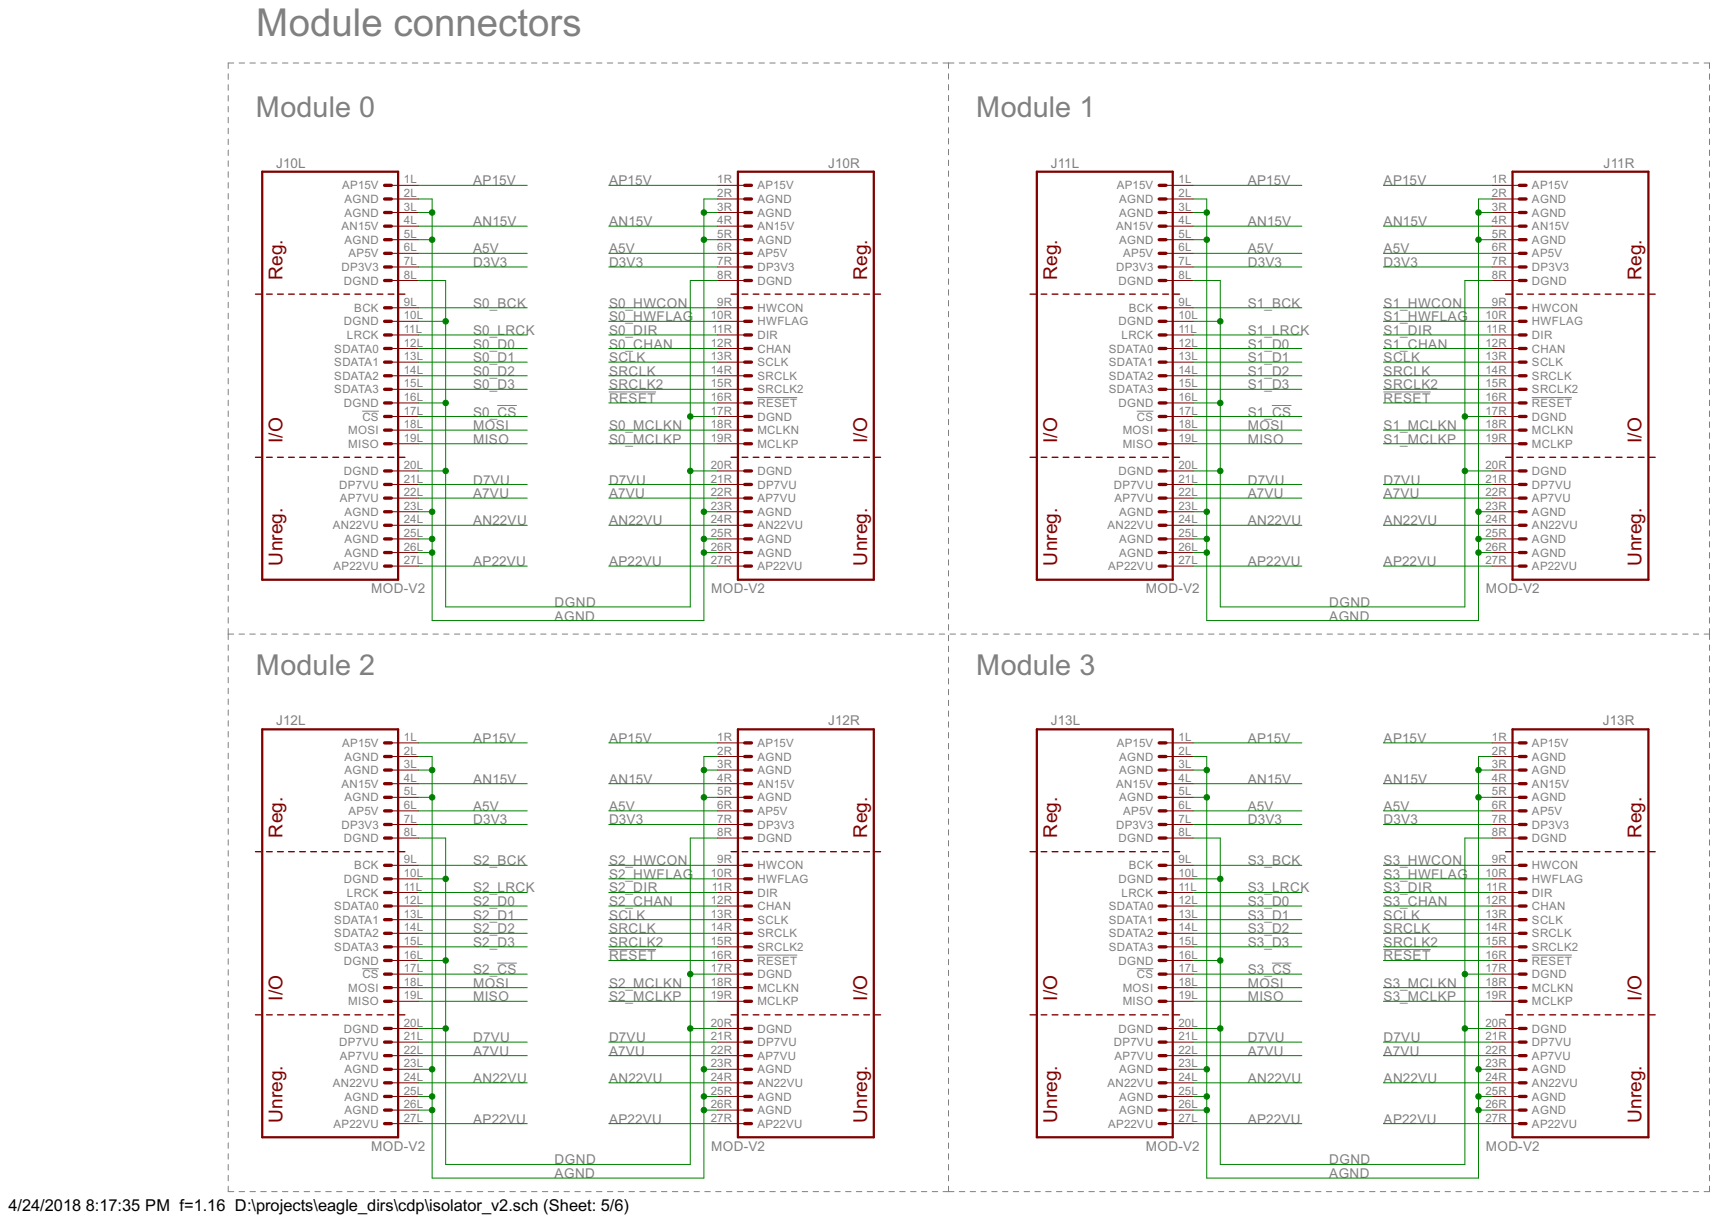
[picture p67: page 5]

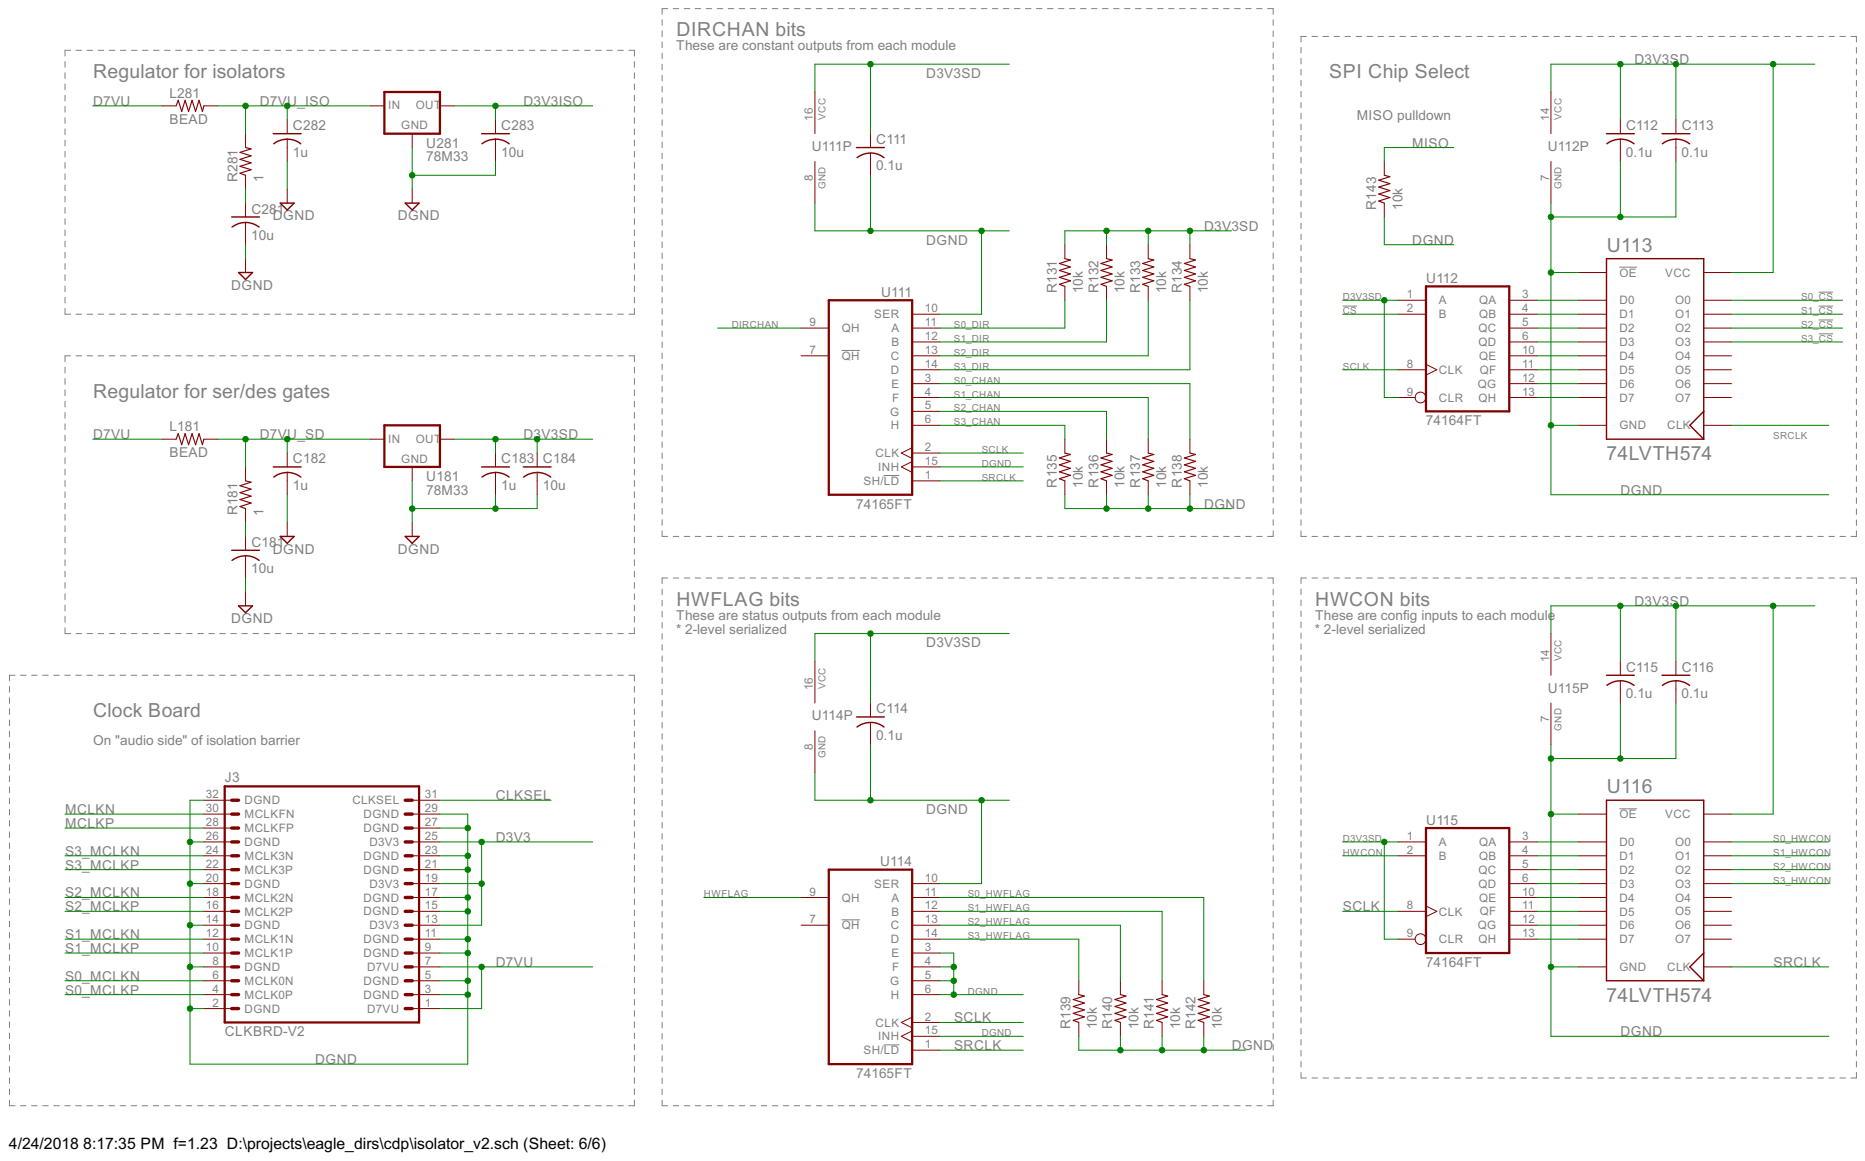
[picture p68: page 6]

DIRCHAN bits
These are constant outputs from each module

Regulator for ser/des gates

GND VCC SH/LD

HWFLAG bits
These are status outputs from each module
* 2-level serialized

HWCON bits
These are config inputs to each module

On "audio side" of isolation barrier

4/24/2018 8:17:35 PM f=1.23 D:\projects\eagle_dirs\cdp\isolator_v2.sch (Sheet: 6/6)
