pricem/da_platform/docs/schematics/psu_v2.pdf

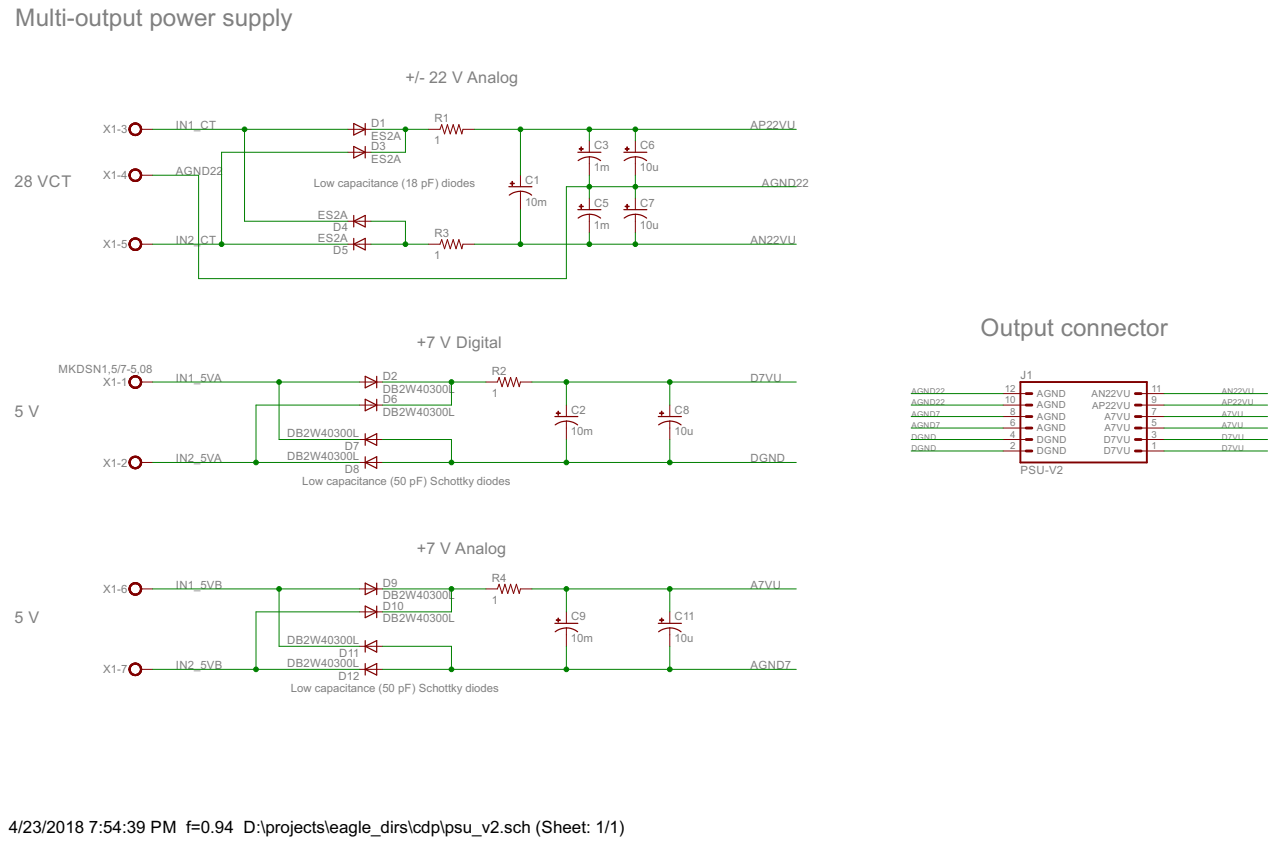
[picture p69: page 1]

Multi-output power supply

Low capacitance (18 pF) diodes

Low capacitance (50 pF) Schottky diodes

4/23/2018 7:54:39 PM f=0.94 D:\projects\eagle_dirs\cdp\psu_v2.sch (Sheet: 1/1)
