pricem/da_platform/docs/figures/hw_arch.pdf

### Carrier

To computer,

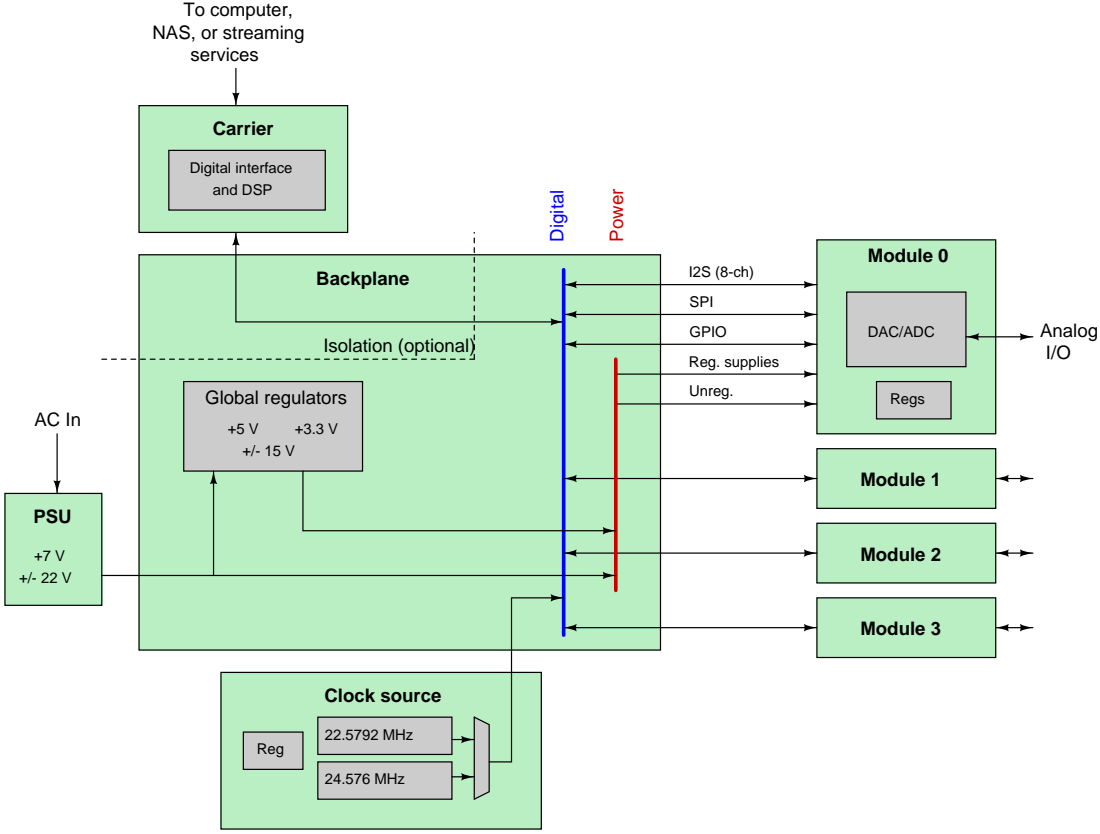
[picture p70: page 1]
Module 0; SPI; GPIO; PSU; Backplane; DAC/ADC; Regs; Reg. supplies; Unreg.; Digital interface; Analog; and DSP; Module 1; Module 2; Module 3; Global regulators; Clock source; Reg; 22.5792 MHz; 24.576 MHz; Digital; Power; Isolation (optional)

NAS, or streaming
services
