pricem/da_platform/docs/schematics/dac2_v1_iv_a.pdf

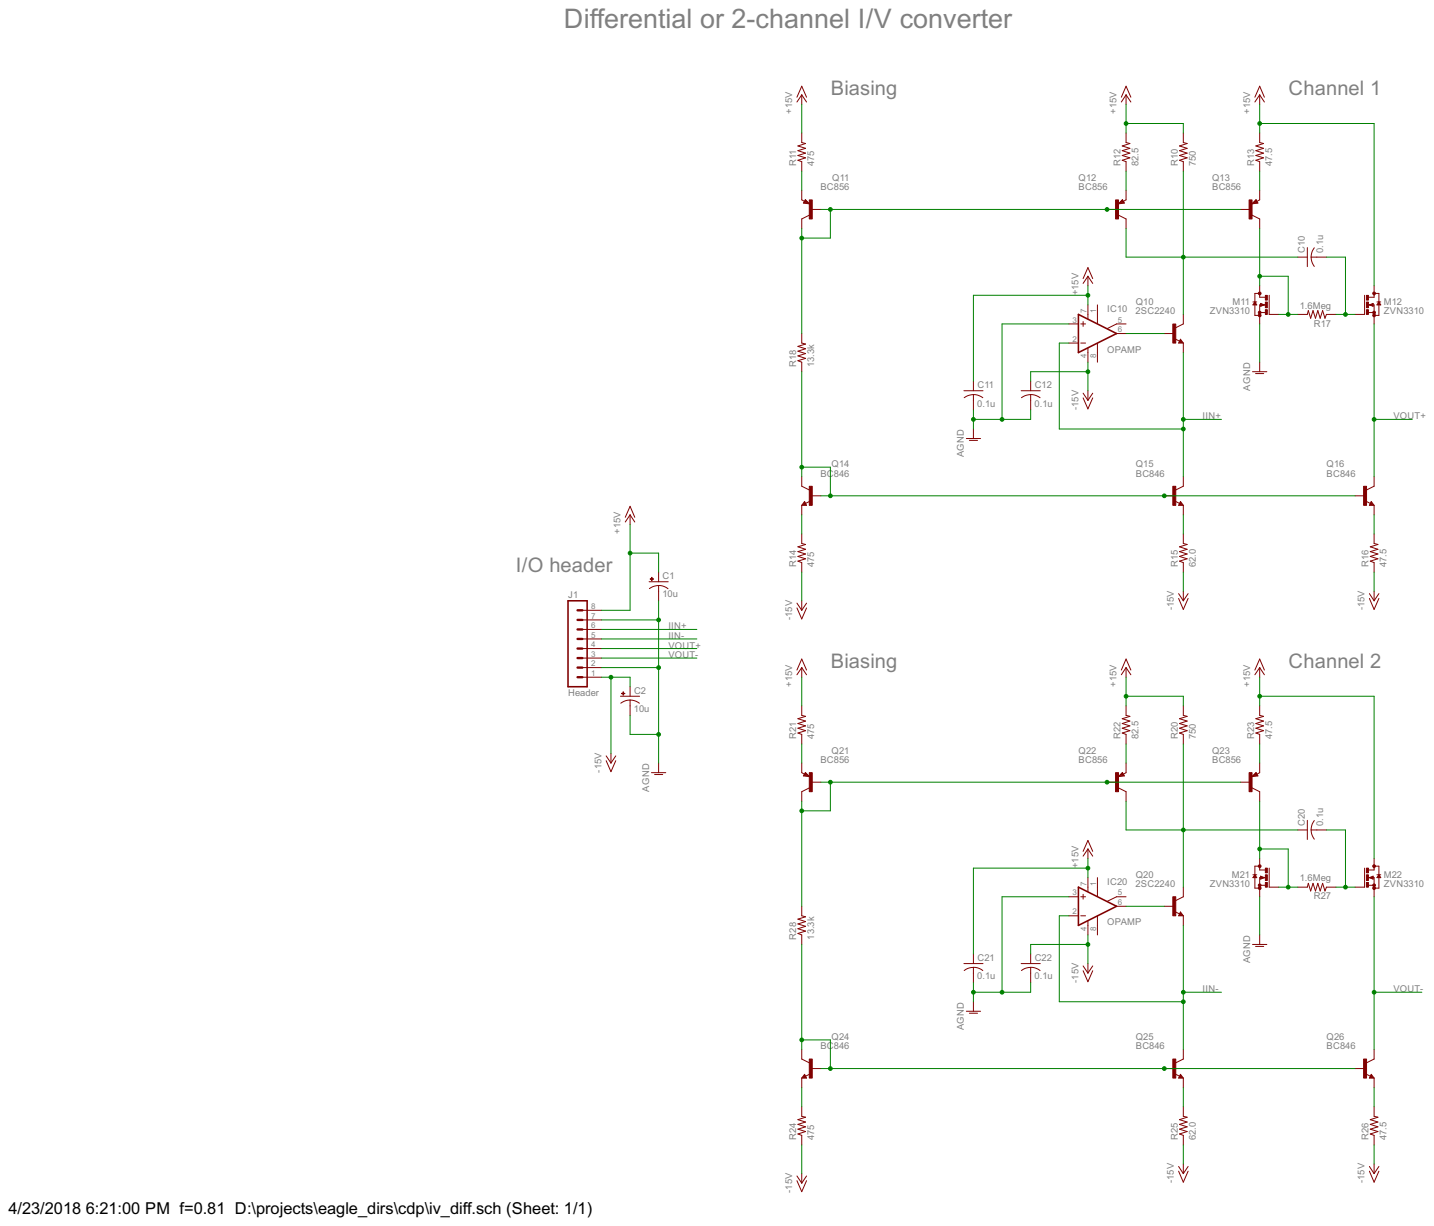
[picture p71: page 1]

Differential or 2-channel I/V converter

4/23/2018 6:21:00 PM f=0.81 D:\projects\eagle_dirs\cdp\iv_diff.sch (Sheet: 1/1)
