pricem/da_platform/docs/figures/dac2_adc2_loopback_fr.pdf

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

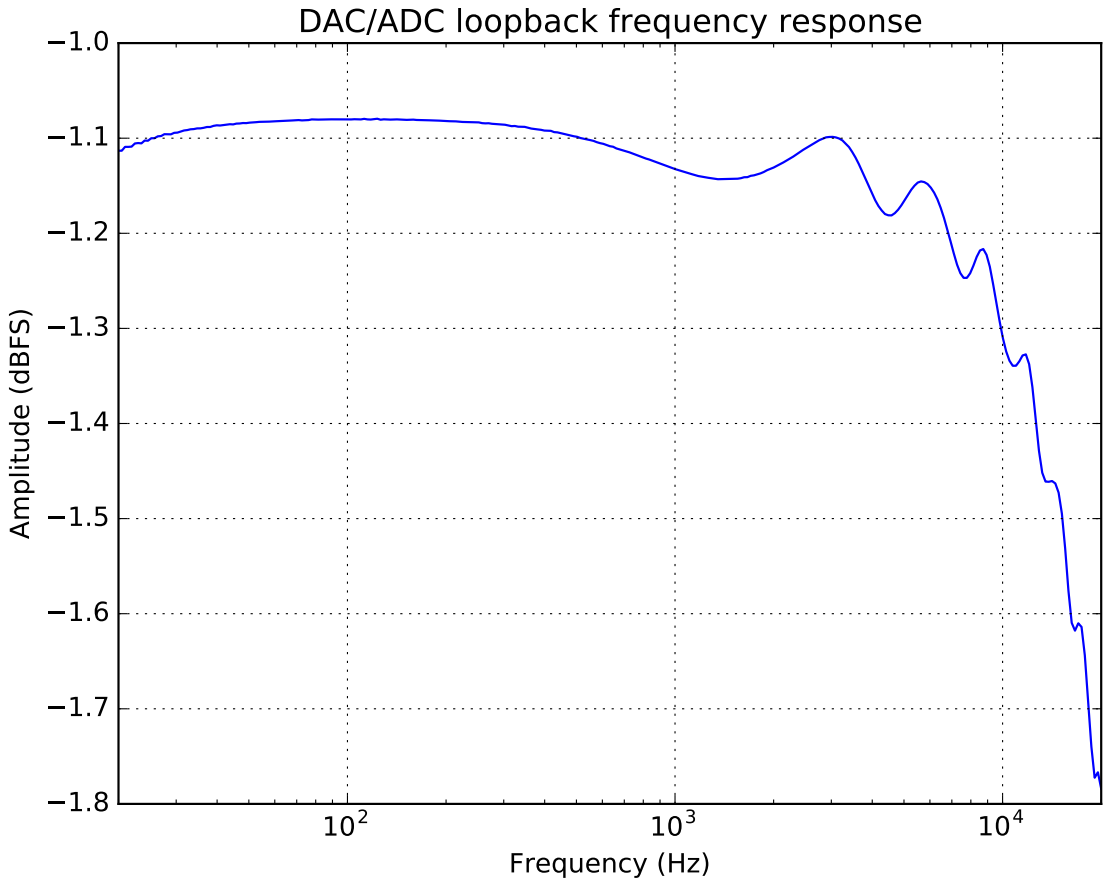
[picture p72: page 1]
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
