pricem/da_platform/docs/figures/dac2_adc2_loopback_m3db_dist_noise.pdf

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

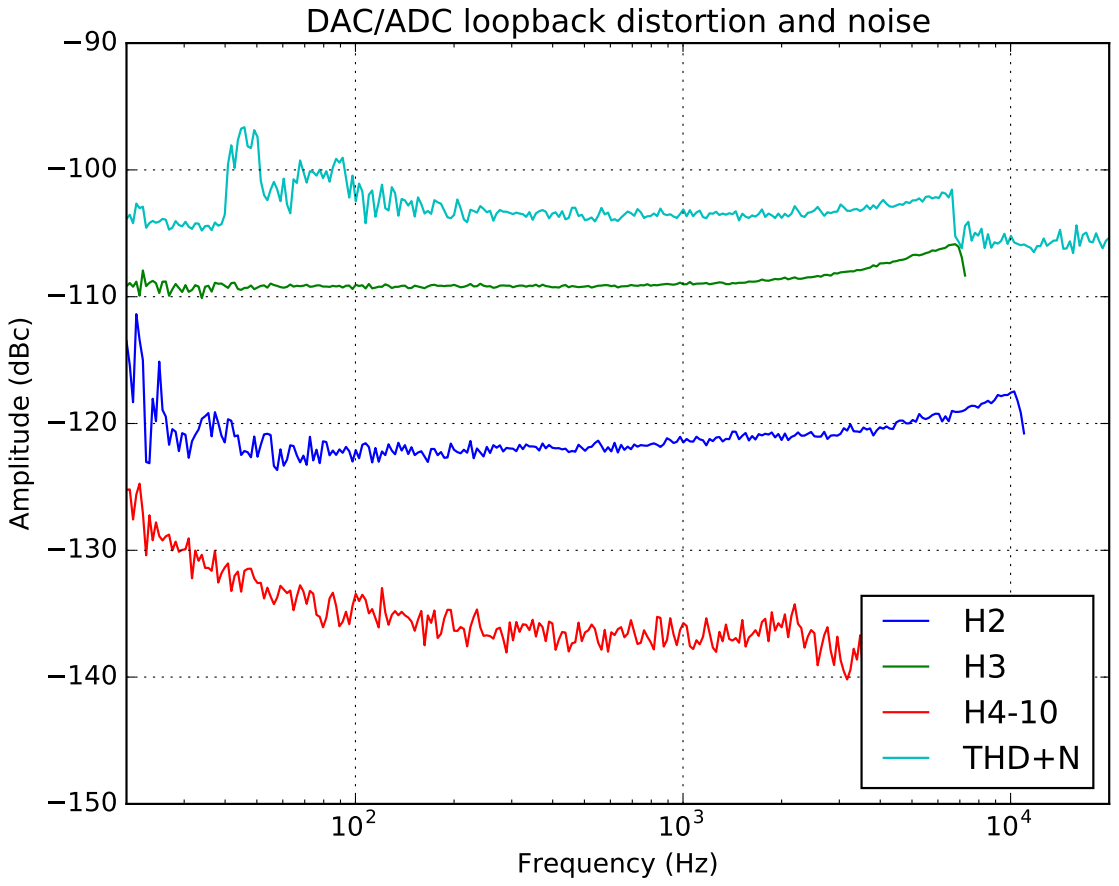
[picture p73: page 1]
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
