pricem/da_platform/docs/figures/dac2_adc2_se_fr.pdf

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

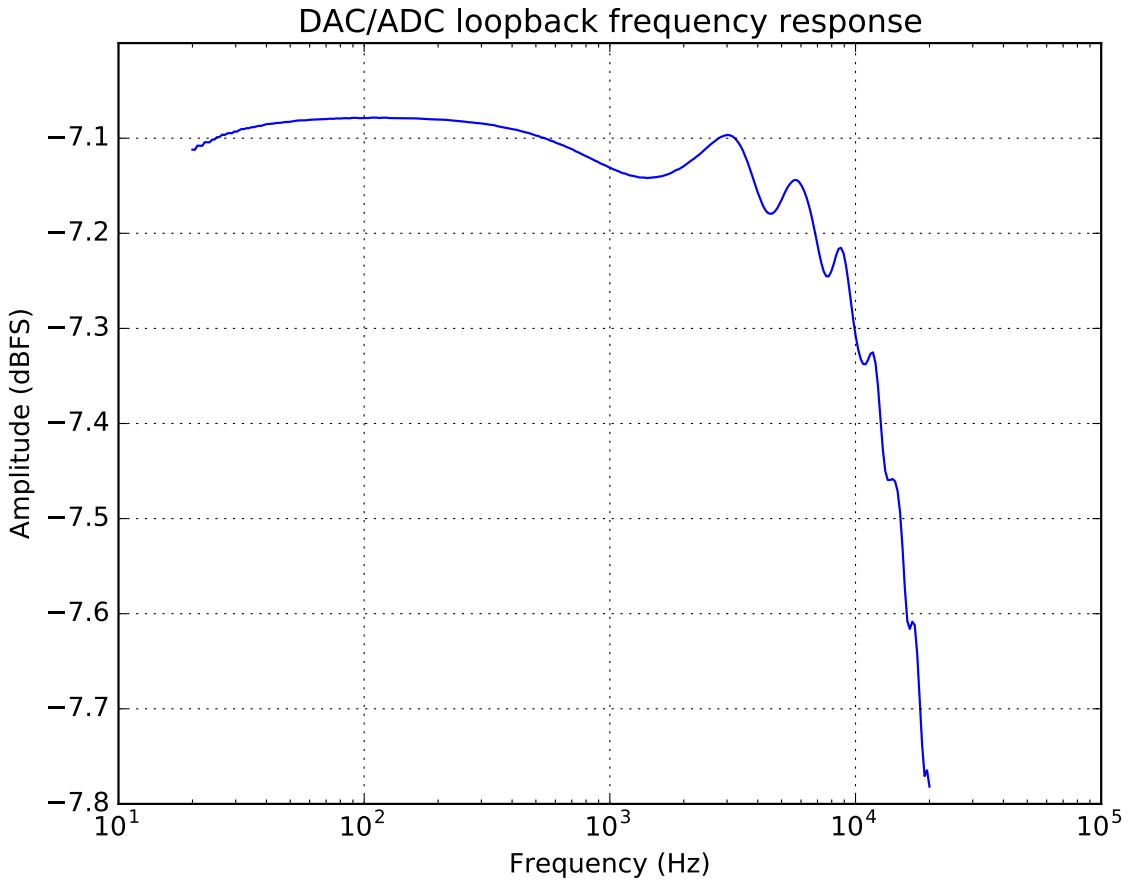
[picture p75: page 1]
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
