pricem/da_platform/docs/figures/dac8_adc8_loopback_att10db_dist_noise.pdf

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

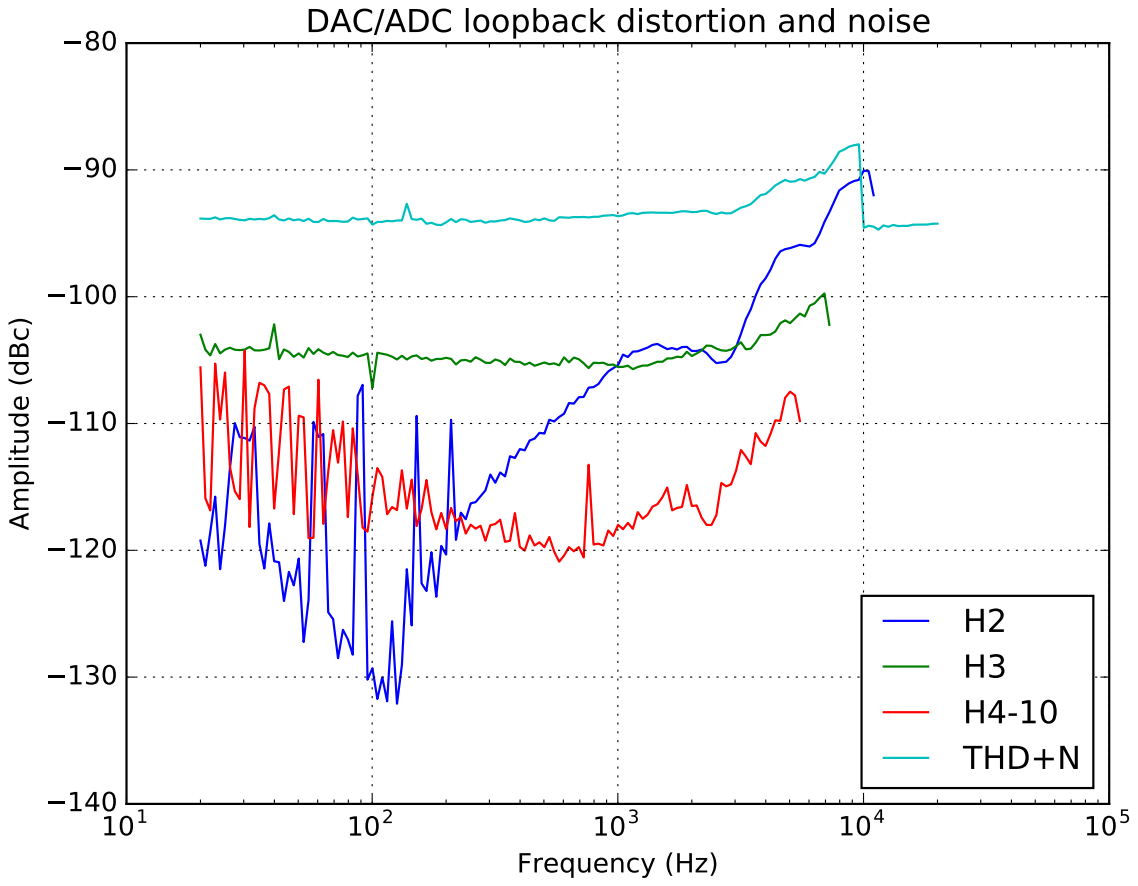
[picture p76: page 1]
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
