pricem/da_platform/docs/plots/8ch_loopback_fullscale.pdf

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

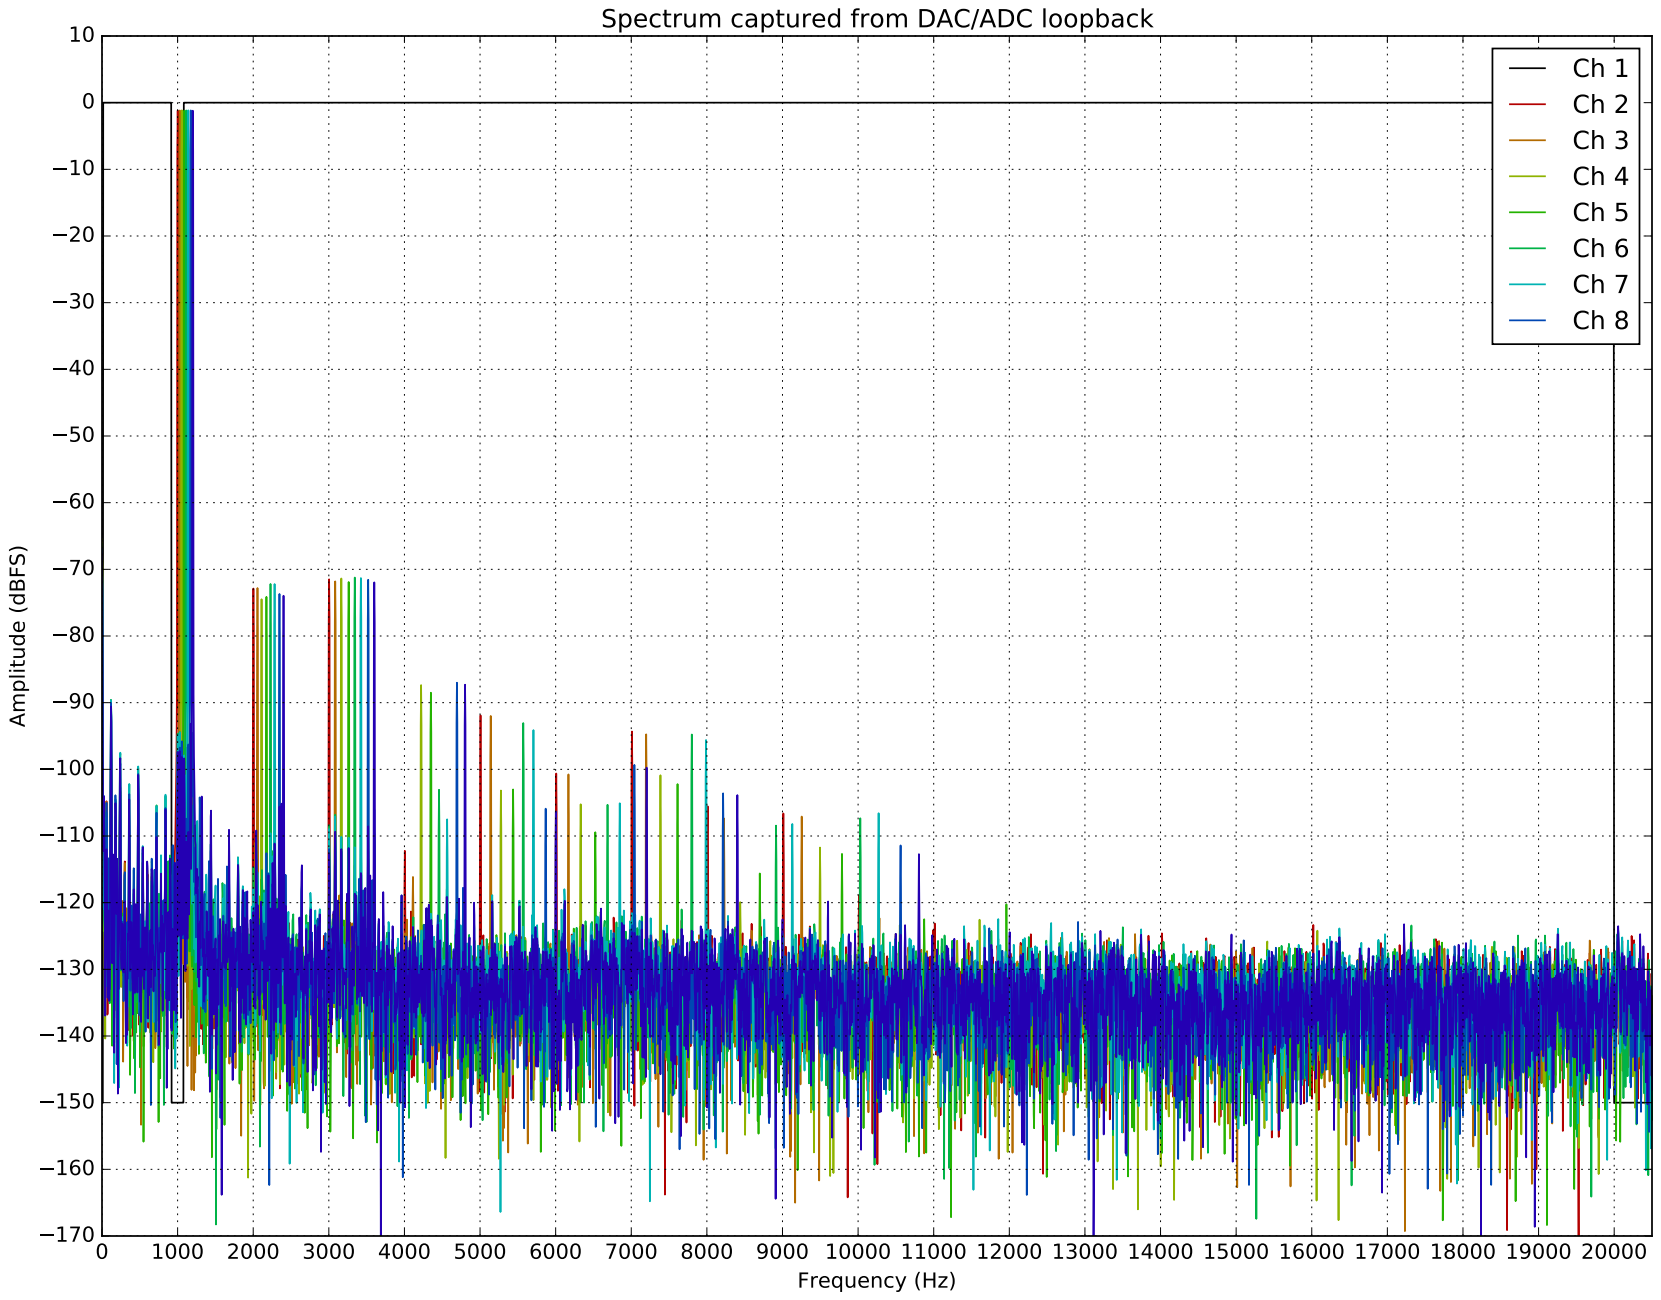
[picture p77: page 1]
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
