pricem/da_platform/docs/plots/loopback_2ch_fft.pdf

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

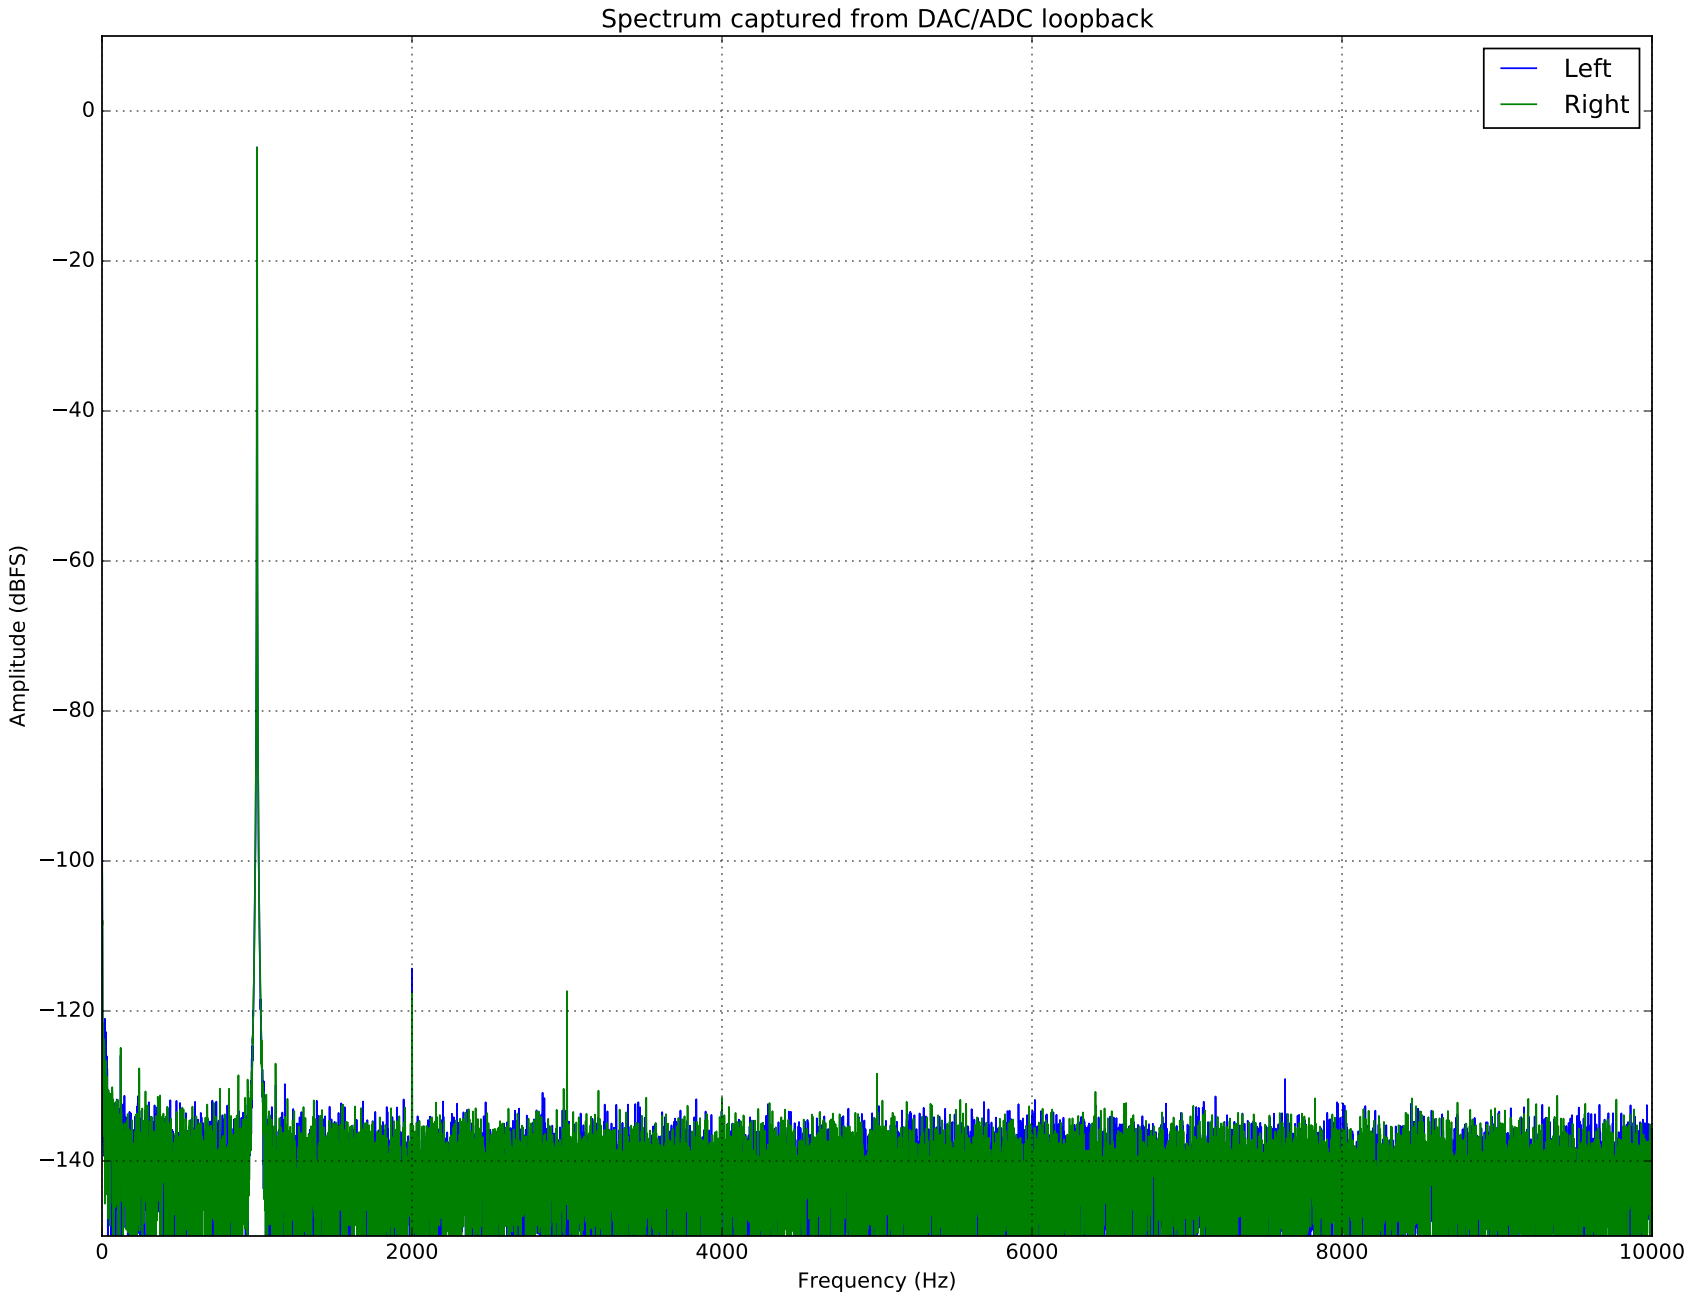
[picture p78: page 1]
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
