pricem/da_platform/docs/schematics/dac2_v1.pdf

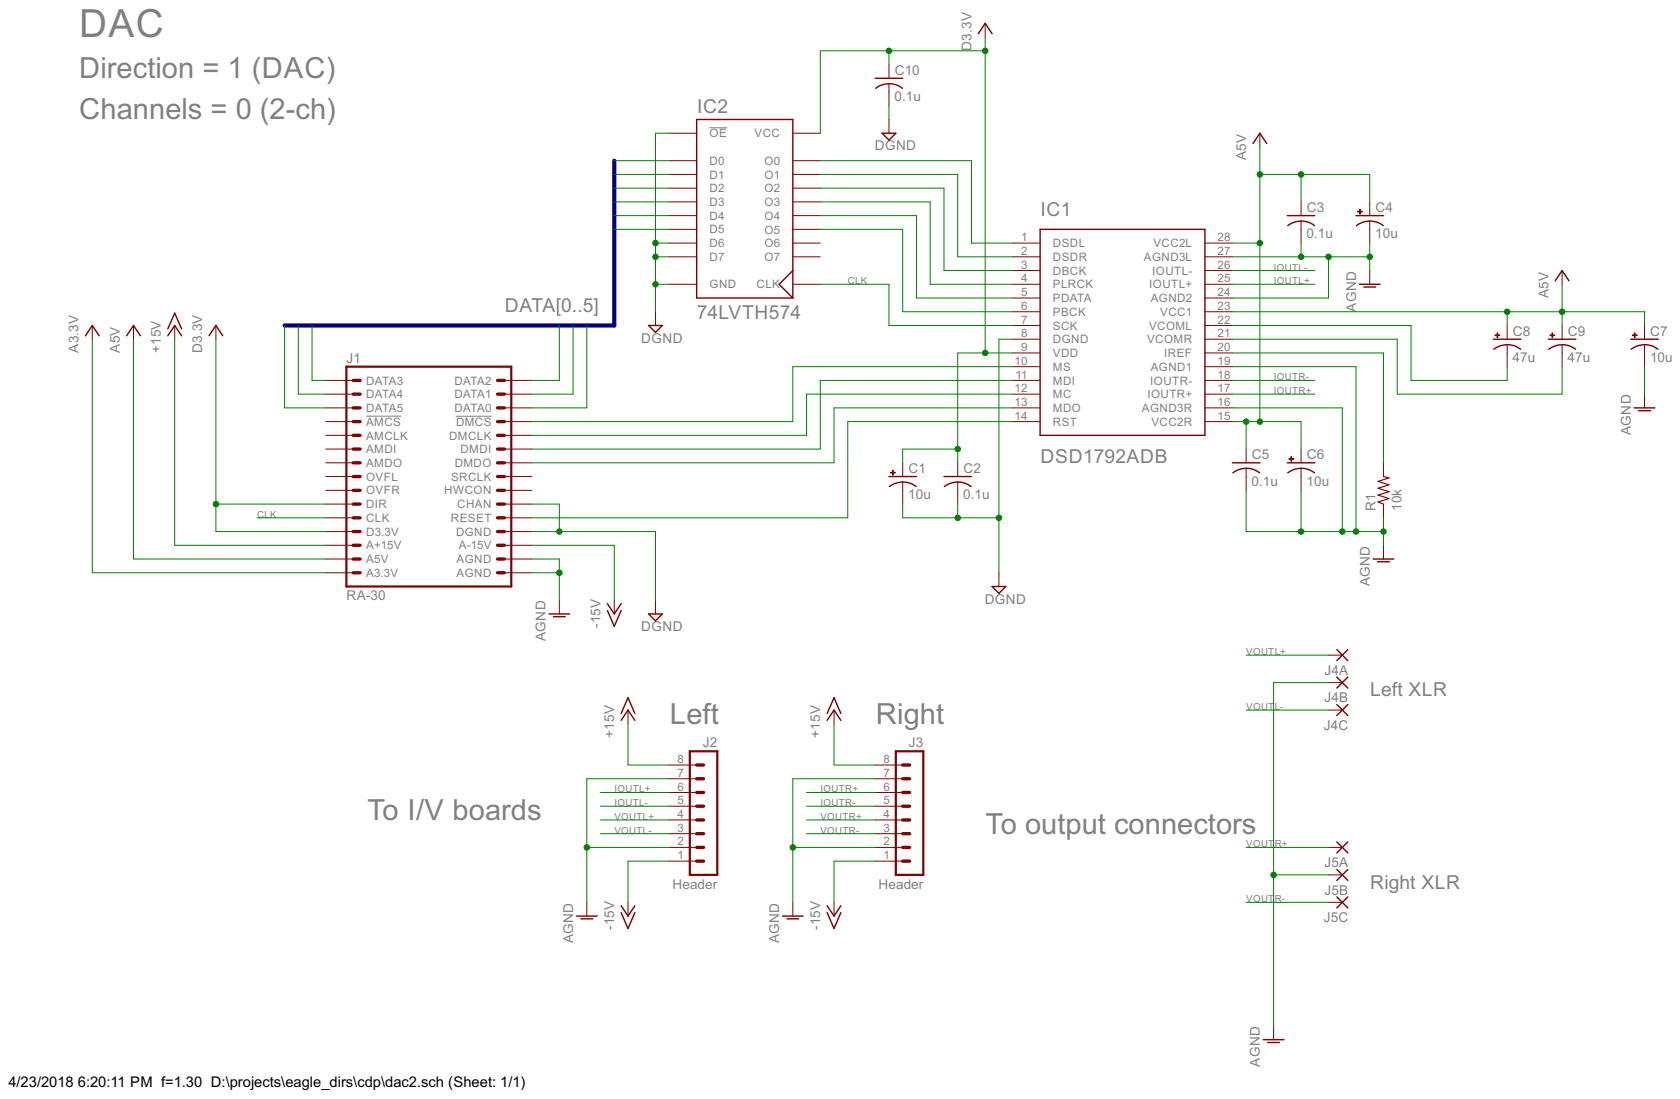
[picture p79: page 1]

6 | 23 AGND2
7 | 22 VCC1

9 | | 20 VCOMR

12
13

15 AGND3R

4/23/2018 6:20:11 PM f=1.30 D:\projects\eagle_dirs\cdp\dac2.sch (Sheet: 1/1)
