pricem/da_platform/docs/schematics/dac8_v1.pdf

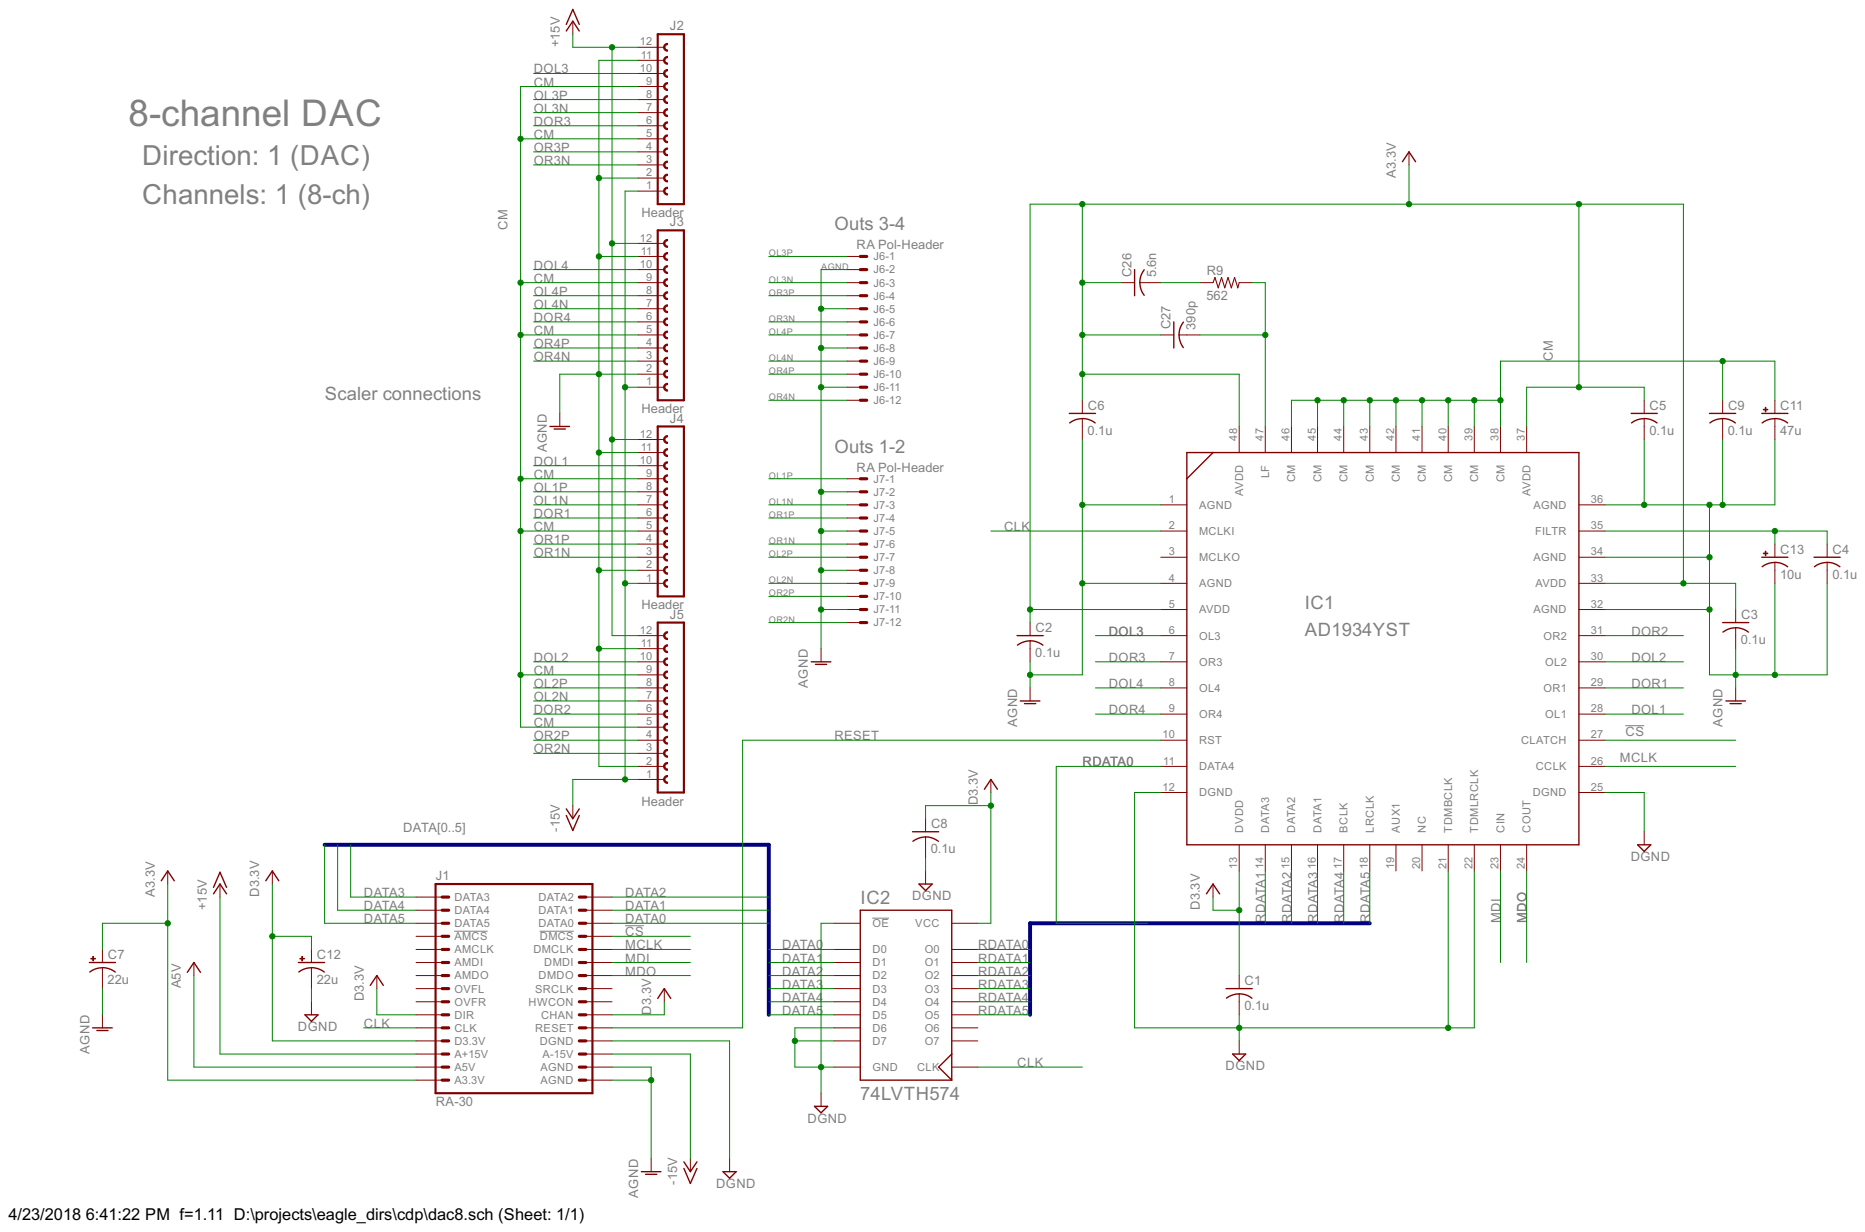
[picture p80: page 1]
