pricem/da_platform/ltspice/iv_v2_rl.asc

C1: cap; 3.3n
C2: cap; 1µ
C3: cap; 10µ
C4: cap; 1.5n
C5: cap; 4.7n
C7: cap; 200p
D1: LED; QTLP690C
D2: LED; QTLP690C
I1: current; SINE(0 -3.9m 1000); AC 1 180
I2: current; SINE(-6.2m 3.9m 1000); AC 1 0
M1: nmos; BSS123
Q1: npn; 2N3904
Q2: npn; 2N3904
Q3: npn; 2N3904
Q4: npn; 2N3904
Q5: npn; BC847B
Q6: pnp; BC556B
Q7: npn; BC546B
Q8: npn; 2N3904
Q9: npn; 2N3904
Q10: pnp; BC857B
Q11: pnp; 2N3906
Q12: npn; 2N3904
Q13: npn; BC546B
Q14: npn; BC546B
Q15: npn; BC546B
Q16: npn; BC546B
Q17: pnp; BC556B
Q18: pnp; BC556B
R1: res; 750
R2: res; 10k
R3: res; 100
R5: res; 10k
R7: res; 600
R8: res; 15
R9: res; 10k
R10: res; 475
R11: res; 15
R12: res; 180
R13: res; 180
R14: res; 1k
R15: res; 1k
R16: res; 1k
R17: res; 1k
R18: res; 100k
R19: res; 82.5
R20: res; 82.5
R21: res; 62
V1: voltage; 15; AC 0
V2: voltage; -15; AC 0
Named nets: 0, Vcc, Vss, IVOut, In, Out, Bufout, Vnb, vca, vcb, vc, Vpb, Vivr, vivr
;tran 0 33m 1m 1.220703125e-7
;op
;noise V(Out) I2 dec 100 0.1 100k
.ac dec 100 1 100meg
;tf V(ivout) I2
;dc I2 -5m 20m 10u
Add RC + other? filtering here
Need to experiment, since the corner freq is high for audio
Add series 1u cap here
Other side of diff pair - power regulator loading
Use some kind of integrated Darlington in place of 2N3904 pairs
Look for low noise, linear current gain through 20 mA (more like 50?)
