pricem/da_platform/ltspice/ad_scaler.asc

C1: cap; 1n
C2: cap; 1n
C3: cap; 1n
R1: res; 1.5k
R2: res; 1.5k
R3: res; 2k
R4: res; 3.52k
R5: res; 3.52k
R6: res; 6.04k
R7: res; 6.04k
V1: voltage; SINE(0 5.66 1000); AC 1 0
V2: voltage; 0
V3: voltage; SINE(0 -5.66 1000); AC 1 180
V4: voltage; 3.3
Named nets: 0, ip, in, aip, ain, 1p, 1n
;op
.ac dec 100 1 1meg
;tran 0 10m 0 1u
Scaler for ADC: 4 V RMS (-5.66 to 5.66 V) -> 0.15 to 2.85 V
