pricem/da_platform/ltspice/iv1.asc

C1: cap; 0.1µ
C2: cap; 200p
I2: current; SINE(-6.2m 3.9m 1000); AC 1 0
M1: nmos; BSS123
M2: nmos; BSS123
Q1: npn; 2N3904
Q2: npn; BC546B
Q3: pnp; BC556B
Q5: npn; BC546B
Q6: pnp; BC556B
Q7: npn; BC546B
R1: res; 750
R2: res; 1.6Meg
R3: res; 10k
R4: res; 475
R5: res; 13.3k
R6: res; 475
R8: res; 62.0
R9: res; 82.5
R10: res; 82.5
U2: UniversalOpamp2
V1: voltage; 15
V2: voltage; -15
Named nets: 0, Vcc, Vss, IVOut, In, Base, Out
;tran 0 10m 0 100n
;op
;noise V(Out) I2 dec 100 0.1 100k
.ac dec 100 10 100meg
;tf V(ivout) I2
;dc I2 -5m 20m 10u
There used to be a BJT and bias resistor here
They have been removed; no need due to DAC output offset
