pricem/da_platform/ltspice/scaler1.asc

C1: cap; 0.1u
C2: cap; 200p
C3: cap; 100p
C4: cap; 0.1u
C5: cap; 200p
M1: nmos; BSS123
M2: nmos; BSS123
M3: nmos; BSS123
Q1: npn; BC546B
Q2: npn; BC546B
Q3: pnp; BC556B
Q4: npn; BC546B
Q5: npn; BC546B
Q6: pnp; BC556B
Q7: npn; BC546B
Q8: npn; BC546B
R1: res; 75
R2: res; 1.6Meg
R3: res; 10k
R4: res; 475
R5: res; 13.3k
R6: res; 475
R7: res; 75
R8: res; 47.5
R9: res; 100
R10: res; 100
R11: res; 750
R12: res; 750
R13: res; 1.6Meg
R14: res; 10k
R15: res; 100
R16: res; 11k
R17: res; 11k
R18: res; 1k
R19: res; 1k
V1: voltage; 15
V2: voltage; -15
V3: voltage; 1.5
V4: voltage; SINE(1.5 1.24 20000); AC 1 0
Named nets: 0, Vcc, Vss, OutA, CM, In, OutB, 1A, 1B, OB
.tran 0 10m 0 100n
;op
;noise V(Out) I2 dec 100 0.1 100k
;ac dec 100 1 1meg
;tf V(ivout) I2
;dc I2 -5m 20m 10u
